CommanderCoder/pico-xb80/sharp-mz80k/mzFiles/BASIC_SP_5025_FD.asm

XOR A                  ;1200 > AF            ¯
LD (3D16H),A           ;1201   32 16 3D      2=
LD (FFFFH),A           ;1204   32 FF FF      2ÿÿ
LD HL,43FFH            ;1207   21 FF 43      !ÿC
LD D,D0H               ;120A   16 D0         Ð
INC HL                 ;120C   23            #
LD A,H                 ;120D   7C            |
CP D                   ;120E   BA            º
JR Z,121BH             ;120F   28 0A         (

LD A,FFH               ;1211   3E FF         >ÿ
LD (HL),A              ;1213   77            w
SUB (HL)               ;1214   96            
JR NZ,121BH            ;1215   20 04          
LD (HL),A              ;1217   77            w
CP (HL)                ;1218   BE            ¾
JR Z,120CH             ;1219   28 F1         (ñ
LD (4561H),HL          ;121B   22 61 45      "aE
LD (4563H),HL          ;121E   22 63 45      "cE
LD SP,HL               ;1221   F9            ù
CALL 0006H             ;1222   CD 06 00      Í
LD DE,12E2H            ;1225   11 E2 12      â
CALL 0015H             ;1228   CD 15 00      Í
CALL 1832H             ;122B   CD 32 18      Í2
LD BC,000AH            ;122E   01 0A 00      

CALL 173FH             ;1231   CD 3F 17      Í?
LD DE,4400H            ;1234   11 00 44      D
PUSH DE                ;1237   D5            Õ
CALL 16F7H             ;1238   CD F7 16      Í÷
POP DE                 ;123B   D1            Ñ
CALL 1357H             ;123C   CD 57 13      ÍW
LD DE,1326H            ;123F   11 26 13      &
CALL 0015H             ;1242   CD 15 00      Í
XOR A                  ;1245   AF            ¯
LD D,A                 ;1246   57            W
LD E,A                 ;1247   5F            _
CALL 0033H             ;1248   CD 33 00      Í3
LD DE,12FEH            ;124B   11 FE 12      þ
CALL 0030H             ;124E   CD 30 00      Í0
LD DE,12F9H            ;1251   11 F9 12      ù
CALL 1357H             ;1254   CD 57 13      ÍW
LD A,(4565H)           ;1257   3A 65 45      :eE
OR A                   ;125A   B7            ·
JP Z,1274H             ;125B   CA 74 12      Êt
LD HL,(47FFH)          ;125E   2A FF 47      *ÿG
LD A,H                 ;1261   7C            |
OR L                   ;1262   B5            µ
JP Z,1278H             ;1263   CA 78 12      Êx
LD BC,0006H            ;1266   01 06 00      
LD DE,4566H            ;1269   11 66 45      fE
LD HL,47FDH            ;126C   21 FD 47      !ýG
CALL 1799H             ;126F   CD 99 17      Í
JR 1278H               ;1272   18 04         
LD HL,(4563H)          ;1274   2A 63 45      *cE
LD SP,HL               ;1277   F9            ù
CALL 184EH             ;1278   CD 4E 18      ÍN
CALL 0009H             ;127B   CD 09 00      Í	
LD DE,4400H            ;127E   11 00 44      D
CALL 0003H             ;1281   CD 03 00      Í
CALL 13CEH             ;1284   CD CE 13      ÍÎ
CALL 1443H             ;1287   CD 43 14      ÍC
LD HL,(4457H)          ;128A   2A 57 44      *WD
LD A,L                 ;128D   7D            }
OR H                   ;128E   B4            ´
JR NZ,12A0H            ;128F   20 0F          
LD HL,4459H            ;1291   21 59 44      !YD
LD (4801H),HL          ;1294   22 01 48      "H
CALL 168BH             ;1297   CD 8B 16      Í
DEC C                  ;129A   0D            
POP HL                 ;129B   E1            á
ADD HL,DE              ;129C   19            
JP 1278H               ;129D   C3 78 12      Ãx
CALL 1987H             ;12A0   CD 87 19      Í
CALL 13C1H             ;12A3   CD C1 13      ÍÁ
CALL 17A5H             ;12A6   CD A5 17      Í¥
CP (HL)                ;12A9   BE            ¾
LD (DE),A              ;12AA   12            
JR NZ,12BEH            ;12AB   20 11          
CALL 17E8H             ;12AD   CD E8 17      Íè
EX DE,HL               ;12B0   EB            ë
CALL 1766H             ;12B1   CD 66 17      Íf
CALL 1651H             ;12B4   CD 51 16      ÍQ
CALL 189CH             ;12B7   CD 9C 18      Í
EX DE,HL               ;12BA   EB            ë
CALL 17E0H             ;12BB   CD E0 17      Íà
LD A,(4459H)           ;12BE   3A 59 44      :YD
CP 0DH                 ;12C1   FE 0D         þ
JP Z,1257H             ;12C3   CA 57 12      ÊW
CALL 17A8H             ;12C6   CD A8 17      Í¨
RL D                   ;12C9   CB 12         Ë
LD (4455H),HL          ;12CB   22 55 44      "UD
EX DE,HL               ;12CE   EB            ë
LD HL,4455H            ;12CF   21 55 44      !UD
CALL 17E8H             ;12D2   CD E8 17      Íè
CALL 1796H             ;12D5   CD 96 17      Í
CALL 189CH             ;12D8   CD 9C 18      Í
EX DE,HL               ;12DB   EB            ë
CALL 17E0H             ;12DC   CD E0 17      Íà
JP 1257H               ;12DF   C3 57 12      ÃW
JR NZ,130EH            ;12E2   20 2A          *
JR NZ,1339H            ;12E4   20 53          S
LD C,B                 ;12E6   48            H
LD B,C                 ;12E7   41            A
LD D,D                 ;12E8   52            R
LD D,B                 ;12E9   50            P
JR NZ,132EH            ;12EA   20 42          B
LD B,C                 ;12EC   41            A
LD D,E                 ;12ED   53            S
LD C,C                 ;12EE   49            I
LD B,E                 ;12EF   43            C
JR NZ,1345H            ;12F0   20 53          S
LD D,B                 ;12F2   50            P
DEC L                  ;12F3   2D            -
DEC (HL)               ;12F4   35            5
JR NC,1329H            ;12F5   30 32         02
DEC (HL)               ;12F7   35            5
DEC C                  ;12F8   0D            
LD D,D                 ;12F9   52            R
LD B,L                 ;12FA   45            E
LD B,C                 ;12FB   41            A
LD B,H                 ;12FC   44            D
LD E,C                 ;12FD   59            Y
DEC C                  ;12FE   0D            
JR NZ,1346H            ;12FF   20 45          E
LD D,D                 ;1301   52            R
LD D,D                 ;1302   52            R
LD C,A                 ;1303   4F            O
LD D,D                 ;1304   52            R
DEC C                  ;1305   0D            
JR NZ,1351H            ;1306   20 49          I
LD C,(HL)              ;1308   4E            N
DEC C                  ;1309   0D            
LD D,E                 ;130A   53            S
LD E,C                 ;130B   59            Y
LD C,(HL)              ;130C   4E            N
LD D,H                 ;130D   54            T
LD B,C                 ;130E   41            A
LD E,B                 ;130F   58            X
DEC C                  ;1310   0D            
LD C,L                 ;1311   4D            M
LD B,L                 ;1312   45            E
LD C,L                 ;1313   4D            M
LD C,A                 ;1314   4F            O
LD D,D                 ;1315   52            R
LD E,C                 ;1316   59            Y
DEC C                  ;1317   0D            
LD B,H                 ;1318   44            D
LD B,C                 ;1319   41            A
LD D,H                 ;131A   54            T
LD B,C                 ;131B   41            A
DEC C                  ;131C   0D            
LD C,L                 ;131D   4D            M
LD C,C                 ;131E   49            I
LD D,E                 ;131F   53            S
LD C,L                 ;1320   4D            M
LD B,C                 ;1321   41            A
LD D,H                 ;1322   54            T
LD B,E                 ;1323   43            C
LD C,B                 ;1324   48            H
DEC C                  ;1325   0D            
JR NZ,136AH            ;1326   20 42          B
LD E,C                 ;1328   59            Y
LD D,H                 ;1329   54            T
LD B,L                 ;132A   45            E
LD D,E                 ;132B   53            S
DEC C                  ;132C   0D            
LD B,D                 ;132D   42            B
LD D,D                 ;132E   52            R
LD B,L                 ;132F   45            E
LD B,C                 ;1330   41            A
LD C,E                 ;1331   4B            K
DEC C                  ;1332   0D            
LD SP,4636H            ;1333   31 36 46      16F
LD C,A                 ;1336   4F            O
LD D,D                 ;1337   52            R
DEC C                  ;1338   0D            
LD SP,4736H            ;1339   31 36 47      16G
LD C,A                 ;133C   4F            O
LD D,E                 ;133D   53            S
LD D,L                 ;133E   55            U
LD B,D                 ;133F   42            B
DEC C                  ;1340   0D            
LD (HL),46H            ;1341   36 46         6F
LD C,(HL)              ;1343   4E            N
DEC C                  ;1344   0D            
LD B,E                 ;1345   43            C
LD C,A                 ;1346   4F            O
LD C,(HL)              ;1347   4E            N
LD D,H                 ;1348   54            T
DEC C                  ;1349   0D            
LD B,(HL)              ;134A   46            F
LD C,C                 ;134B   49            I
LD C,H                 ;134C   4C            L
LD B,L                 ;134D   45            E
DEC C                  ;134E   0D            
LD C,A                 ;134F   4F            O
LD D,(HL)              ;1350   56            V
LD B,L                 ;1351   45            E
LD D,D                 ;1352   52            R
LD C,H                 ;1353   4C            L
LD B,C                 ;1354   41            A
LD E,C                 ;1355   59            Y
DEC C                  ;1356   0D            
CALL 0009H             ;1357   CD 09 00      Í	
JP 0015H               ;135A   C3 15 00      Ã
CALL 187CH             ;135D   CD 7C 18      Í|
CALL 1357H             ;1360   CD 57 13      ÍW
LD DE,12FFH            ;1363   11 FF 12      ÿ
CALL 0015H             ;1366   CD 15 00      Í
LD HL,(47FFH)          ;1369   2A FF 47      *ÿG
LD A,L                 ;136C   7D            }
OR H                   ;136D   B4            ´
JP Z,124BH             ;136E   CA 4B 12      ÊK
LD DE,4400H            ;1371   11 00 44      D
PUSH DE                ;1374   D5            Õ
CALL 16F7H             ;1375   CD F7 16      Í÷
LD DE,1306H            ;1378   11 06 13      
CALL 0015H             ;137B   CD 15 00      Í
POP DE                 ;137E   D1            Ñ
CALL 0015H             ;137F   CD 15 00      Í
JP 124BH               ;1382   C3 4B 12      ÃK
CALL 0009H             ;1385   CD 09 00      Í	
LD DE,132DH            ;1388   11 2D 13      -
JP 1366H               ;138B   C3 66 13      Ãf
LD DE,130AH            ;138E   11 0A 13      

JR 1396H               ;1391   18 03         
LD DE,1311H            ;1393   11 11 13      
JR 139BH               ;1396   18 03         
LD DE,1318H            ;1398   11 18 13      
JR 13A0H               ;139B   18 03         
LD DE,131DH            ;139D   11 1D 13      

JR 13A5H               ;13A0   18 03         
LD DE,1333H            ;13A2   11 33 13      3
JR 13AAH               ;13A5   18 03         
LD DE,1339H            ;13A7   11 39 13      9
JR 13AFH               ;13AA   18 03         
LD DE,1341H            ;13AC   11 41 13      A
JR 13B4H               ;13AF   18 03         
LD DE,134AH            ;13B1   11 4A 13      J
JR 13B9H               ;13B4   18 03         
LD DE,134FH            ;13B6   11 4F 13      O
JR 13BEH               ;13B9   18 03         
LD DE,1345H            ;13BB   11 45 13      E
JP 135DH               ;13BE   C3 5D 13      Ã]
XOR A                  ;13C1   AF            ¯
JR 13C6H               ;13C2   18 02         
LD A,01H               ;13C4   3E 01         >
JR 13CAH               ;13C6   18 02         
LD A,02H               ;13C8   3E 02         >
LD (4565H),A           ;13CA   32 65 45      2eE
RET                    ;13CD   C9            É
LD HL,4400H            ;13CE   21 00 44      !D
CALL 16F1H             ;13D1   CD F1 16      Íñ
EX DE,HL               ;13D4   EB            ë
LD (4457H),HL          ;13D5   22 57 44      "WD
LD HL,4459H            ;13D8   21 59 44      !YD
LD C,00H               ;13DB   0E 00         
EX DE,HL               ;13DD   EB            ë
CALL 162DH             ;13DE   CD 2D 16      Í-
CALL 1491H             ;13E1   CD 91 14      Í
RET Z                  ;13E4   C8            È
DEC DE                 ;13E5   1B            
CP 3FH                 ;13E6   FE 3F         þ?
JR NZ,13F0H            ;13E8   20 06          
LD A,85H               ;13EA   3E 85         >

LD (DE),A              ;13EC   12            
INC DE                 ;13ED   13            
JR 13E1H               ;13EE   18 F1         ñ
DEC HL                 ;13F0   2B            +
EX DE,HL               ;13F1   EB            ë
PUSH HL                ;13F2   E5            å
LD HL,14D8H            ;13F3   21 D8 14      !Ø
LD B,80H               ;13F6   06 80         
PUSH DE                ;13F8   D5            Õ
CALL 162DH             ;13F9   CD 2D 16      Í-
EX DE,HL               ;13FC   EB            ë
CALL 162DH             ;13FD   CD 2D 16      Í-
EX DE,HL               ;1400   EB            ë
CP (HL)                ;1401   BE            ¾
INC HL                 ;1402   23            #
INC DE                 ;1403   13            
JR Z,13F9H             ;1404   28 F3         (ó
DEC HL                 ;1406   2B            +
CP FFH                 ;1407   FE FF         þÿ
JP Z,1415H             ;1409   CA 15 14      Ê
ADD A,80H              ;140C   C6 80         Æ
JP C,138EH             ;140E   DA 8E 13      Ú
CP (HL)                ;1411   BE            ¾
JP Z,1427H             ;1412   CA 27 14      Ê'
INC B                  ;1415   04            
LD A,DCH               ;1416   3E DC         >Ü
CP B                   ;1418   B8            ¸
JP Z,143BH             ;1419   CA 3B 14      Ê;
LD A,7FH               ;141C   3E 7F         >
CP (HL)                ;141E   BE            ¾
INC HL                 ;141F   23            #
JP NC,141EH            ;1420   D2 1E 14      Ò

POP DE                 ;1423   D1            Ñ
JP 13F8H               ;1424   C3 F8 13      Ãø
POP AF                 ;1427   F1            ñ
POP HL                 ;1428   E1            á
LD (HL),B              ;1429   70            p
INC HL                 ;142A   23            #
EX DE,HL               ;142B   EB            ë
LD A,B                 ;142C   78            x
CP 82H                 ;142D   FE 82         þ
JP NC,13E1H            ;142F   D2 E1 13      Òá
CALL 14C5H             ;1432   CD C5 14      ÍÅ
CP 3AH                 ;1435   FE 3A         þ:
JP Z,13E1H             ;1437   CA E1 13      Êá
RET                    ;143A   C9            É
POP DE                 ;143B   D1            Ñ
POP HL                 ;143C   E1            á
INC DE                 ;143D   13            
INC HL                 ;143E   23            #
EX DE,HL               ;143F   EB            ë
JP 13E1H               ;1440   C3 E1 13      Ãá
LD HL,(4457H)          ;1443   2A 57 44      *WD
LD DE,4400H            ;1446   11 00 44      D
LD C,B2H               ;1449   0E B2         ²
CALL 16F9H             ;144B   CD F9 16      Íù
LD A,20H               ;144E   3E 20         > 
LD (DE),A              ;1450   12            
INC DE                 ;1451   13            
LD HL,4459H            ;1452   21 59 44      !YD
CALL 1491H             ;1455   CD 91 14      Í
RET Z                  ;1458   C8            È
SUB 80H                ;1459   D6 80         Ö
JP M,1455H             ;145B   FA 55 14      úU
DEC C                  ;145E   0D            
PUSH AF                ;145F   F5            õ
DEC DE                 ;1460   1B            
PUSH HL                ;1461   E5            å
LD HL,14D8H            ;1462   21 D8 14      !Ø
OR A                   ;1465   B7            ·
JP Z,1475H             ;1466   CA 75 14      Êu
PUSH AF                ;1469   F5            õ
LD A,7FH               ;146A   3E 7F         >
CP (HL)                ;146C   BE            ¾
INC HL                 ;146D   23            #
JR NC,146CH            ;146E   30 FC         0ü
POP AF                 ;1470   F1            ñ
DEC A                  ;1471   3D            =
JP 1465H               ;1472   C3 65 14      Ãe
CALL 14BAH             ;1475   CD BA 14      Íº
OR A                   ;1478   B7            ·
JP P,1475H             ;1479   F2 75 14      òu
DEC DE                 ;147C   1B            
AND 7FH                ;147D   E6 7F         æ
LD (DE),A              ;147F   12            
INC DE                 ;1480   13            
POP HL                 ;1481   E1            á
POP AF                 ;1482   F1            ñ
CP 02H                 ;1483   FE 02         þ
JP NC,1455H            ;1485   D2 55 14      ÒU
CALL 14C5H             ;1488   CD C5 14      ÍÅ
CP 3AH                 ;148B   FE 3A         þ:
JP Z,1455H             ;148D   CA 55 14      ÊU
RET                    ;1490   C9            É
CALL 14BAH             ;1491   CD BA 14      Íº
RET Z                  ;1494   C8            È
CALL 14A5H             ;1495   CD A5 14      Í¥
JR Z,1491H             ;1498   28 F7         (÷
CP 22H                 ;149A   FE 22         þ"
RET NZ                 ;149C   C0            À
CALL 14B1H             ;149D   CD B1 14      Í±
CP 0DH                 ;14A0   FE 0D         þ
JR NZ,1491H            ;14A2   20 ED          í
RET                    ;14A4   C9            É
CP 20H                 ;14A5   FE 20         þ 
RET Z                  ;14A7   C8            È
CP FFH                 ;14A8   FE FF         þÿ
RET Z                  ;14AA   C8            È
CP 28H                 ;14AB   FE 28         þ(
RET Z                  ;14AD   C8            È
CP 29H                 ;14AE   FE 29         þ)
RET                    ;14B0   C9            É
CALL 14BAH             ;14B1   CD BA 14      Íº
RET Z                  ;14B4   C8            È
CP 22H                 ;14B5   FE 22         þ"
JR NZ,14B1H            ;14B7   20 F8          ø
RET                    ;14B9   C9            É
LD A,(HL)              ;14BA   7E            ~
LD (DE),A              ;14BB   12            
INC HL                 ;14BC   23            #
INC DE                 ;14BD   13            
INC C                  ;14BE   0C            

JP Z,1398H             ;14BF   CA 98 13      Ê
CP 0DH                 ;14C2   FE 0D         þ
RET                    ;14C4   C9            É
CALL 14BAH             ;14C5   CD BA 14      Íº
RET Z                  ;14C8   C8            È
CP 3AH                 ;14C9   FE 3A         þ:
RET Z                  ;14CB   C8            È
CP 22H                 ;14CC   FE 22         þ"
JR NZ,14C5H            ;14CE   20 F5          õ
CALL 14B1H             ;14D0   CD B1 14      Í±
CP 0DH                 ;14D3   FE 0D         þ
JR NZ,14C5H            ;14D5   20 EE          î
RET                    ;14D7   C9            É
LD D,D                 ;14D8   52            R
LD B,L                 ;14D9   45            E
CALL 4144H             ;14DA   CD 44 41      ÍDA
LD D,H                 ;14DD   54            T
POP BC                 ;14DE   C1            Á
LD C,H                 ;14DF   4C            L
LD C,C                 ;14E0   49            I
LD D,E                 ;14E1   53            S
CALL NC,5552H          ;14E2   D4 52 55      ÔRU
ADC A,4EH              ;14E5   CE 4E         ÎN
LD B,L                 ;14E7   45            E
RST 10H                ;14E8   D7            ×
LD D,B                 ;14E9   50            P
LD D,D                 ;14EA   52            R
LD C,C                 ;14EB   49            I
LD C,(HL)              ;14EC   4E            N
CALL NC,454CH          ;14ED   D4 4C 45      ÔLE
CALL NC,4F46H          ;14F0   D4 46 4F      ÔFO
JP NC,C649H            ;14F3   D2 49 C6      ÒIÆ
LD B,A                 ;14F6   47            G
LD C,A                 ;14F7   4F            O
LD D,H                 ;14F8   54            T
RST 08H                ;14F9   CF            Ï
LD D,D                 ;14FA   52            R
LD B,L                 ;14FB   45            E
LD B,C                 ;14FC   41            A
CALL NZ,4F47H          ;14FD   C4 47 4F      ÄGO
LD D,E                 ;1500   53            S
LD D,L                 ;1501   55            U
JP NZ,4552H            ;1502   C2 52 45      ÂRE
LD D,H                 ;1505   54            T
LD D,L                 ;1506   55            U
LD D,D                 ;1507   52            R
ADC A,4EH              ;1508   CE 4E         ÎN
LD B,L                 ;150A   45            E
LD E,B                 ;150B   58            X
CALL NC,5453H          ;150C   D4 53 54      ÔST
LD C,A                 ;150F   4F            O
RET NC                 ;1510   D0            Ð
LD B,L                 ;1511   45            E
LD C,(HL)              ;1512   4E            N
CALL NZ,CE4FH          ;1513   C4 4F CE      ÄOÎ
LD C,H                 ;1516   4C            L
LD C,A                 ;1517   4F            O
LD B,C                 ;1518   41            A
CALL NZ,4153H          ;1519   C4 53 41      ÄSA
LD D,(HL)              ;151C   56            V
PUSH BC                ;151D   C5            Å
LD D,(HL)              ;151E   56            V
LD B,L                 ;151F   45            E
LD D,D                 ;1520   52            R
LD C,C                 ;1521   49            I
LD B,(HL)              ;1522   46            F
EXX                    ;1523   D9            Ù
LD D,B                 ;1524   50            P
LD C,A                 ;1525   4F            O
LD C,E                 ;1526   4B            K
PUSH BC                ;1527   C5            Å
LD B,H                 ;1528   44            D
LD C,C                 ;1529   49            I
CALL 4544H             ;152A   CD 44 45      ÍDE
LD B,(HL)              ;152D   46            F
JR NZ,1576H            ;152E   20 46          F
ADC A,49H              ;1530   CE 49         ÎI
LD C,(HL)              ;1532   4E            N
LD D,B                 ;1533   50            P
LD D,L                 ;1534   55            U
CALL NC,4552H          ;1535   D4 52 45      ÔRE
LD D,E                 ;1538   53            S
LD D,H                 ;1539   54            T
LD C,A                 ;153A   4F            O
LD D,D                 ;153B   52            R
PUSH BC                ;153C   C5            Å
LD B,E                 ;153D   43            C
LD C,H                 ;153E   4C            L
JP NC,554DH            ;153F   D2 4D 55      ÒMU
LD D,E                 ;1542   53            S
LD C,C                 ;1543   49            I
JP 4554H               ;1544   C3 54 45      ÃTE
LD C,L                 ;1547   4D            M
LD D,B                 ;1548   50            P
RST 08H                ;1549   CF            Ï
LD D,L                 ;154A   55            U
LD D,E                 ;154B   53            S
LD D,D                 ;154C   52            R
XOR B                  ;154D   A8            ¨
LD D,A                 ;154E   57            W
LD C,A                 ;154F   4F            O
LD D,B                 ;1550   50            P
LD B,L                 ;1551   45            E
ADC A,52H              ;1552   CE 52         ÎR
LD C,A                 ;1554   4F            O
LD D,B                 ;1555   50            P
LD B,L                 ;1556   45            E
ADC A,43H              ;1557   CE 43         ÎC
LD C,H                 ;1559   4C            L
LD C,A                 ;155A   4F            O
LD D,E                 ;155B   53            S
PUSH BC                ;155C   C5            Å
LD B,D                 ;155D   42            B
LD E,C                 ;155E   59            Y
PUSH BC                ;155F   C5            Å
LD C,H                 ;1560   4C            L
LD C,C                 ;1561   49            I
LD C,L                 ;1562   4D            M
LD C,C                 ;1563   49            I
CALL NC,4F43H          ;1564   D4 43 4F      ÔCO
LD C,(HL)              ;1567   4E            N
CALL NC,4553H          ;1568   D4 53 45      ÔSE
CALL NC,4552H          ;156B   D4 52 45      ÔRE
LD D,E                 ;156E   53            S
LD B,L                 ;156F   45            E
CALL NC,4547H          ;1570   D4 47 45      ÔGE
CALL NC,4E49H          ;1573   D4 49 4E      ÔIN
LD D,B                 ;1576   50            P
AND E                  ;1577   A3            £
LD C,A                 ;1578   4F            O
LD D,L                 ;1579   55            U
LD D,H                 ;157A   54            T
AND E                  ;157B   A3            £
RST 38H                ;157C   FF            ÿ
RST 38H                ;157D   FF            ÿ
RST 38H                ;157E   FF            ÿ
RST 38H                ;157F   FF            ÿ
RST 38H                ;1580   FF            ÿ
LD D,H                 ;1581   54            T
LD C,B                 ;1582   48            H
LD B,L                 ;1583   45            E
ADC A,54H              ;1584   CE 54         ÎT
RST 08H                ;1586   CF            Ï
LD D,E                 ;1587   53            S
LD D,H                 ;1588   54            T
LD B,L                 ;1589   45            E
RET NC                 ;158A   D0            Ð
LD A,BCH               ;158B   3E BC         >¼
INC A                  ;158D   3C            <
CP (HL)                ;158E   BE            ¾
DEC A                  ;158F   3D            =
CP H                   ;1590   BC            ¼
INC A                  ;1591   3C            <
CP L                   ;1592   BD            ½
DEC A                  ;1593   3D            =
CP (HL)                ;1594   BE            ¾
LD A,BDH               ;1595   3E BD         >½
CP L                   ;1597   BD            ½
CP (HL)                ;1598   BE            ¾
CP H                   ;1599   BC            ¼
LD B,C                 ;159A   41            A
LD C,(HL)              ;159B   4E            N
CALL NZ,D24FH          ;159C   C4 4F D2      ÄOÒ
LD C,(HL)              ;159F   4E            N
LD C,A                 ;15A0   4F            O
CALL NC,ADABH          ;15A1   D4 AB AD      Ô«­
XOR D                  ;15A4   AA            ª
XOR A                  ;15A5   AF            ¯
LD C,H                 ;15A6   4C            L
LD B,L                 ;15A7   45            E
LD B,(HL)              ;15A8   46            F
LD D,H                 ;15A9   54            T
INC H                  ;15AA   24            $
XOR B                  ;15AB   A8            ¨
LD D,D                 ;15AC   52            R
LD C,C                 ;15AD   49            I
LD B,A                 ;15AE   47            G
LD C,B                 ;15AF   48            H
LD D,H                 ;15B0   54            T
INC H                  ;15B1   24            $
XOR B                  ;15B2   A8            ¨
LD C,L                 ;15B3   4D            M
LD C,C                 ;15B4   49            I
LD B,H                 ;15B5   44            D
INC H                  ;15B6   24            $
XOR B                  ;15B7   A8            ¨
LD C,H                 ;15B8   4C            L
LD B,L                 ;15B9   45            E
LD C,(HL)              ;15BA   4E            N
XOR B                  ;15BB   A8            ¨
LD B,E                 ;15BC   43            C
LD C,B                 ;15BD   48            H
LD D,D                 ;15BE   52            R
INC H                  ;15BF   24            $
XOR B                  ;15C0   A8            ¨
LD D,E                 ;15C1   53            S
LD D,H                 ;15C2   54            T
LD D,D                 ;15C3   52            R
INC H                  ;15C4   24            $
XOR B                  ;15C5   A8            ¨
LD B,C                 ;15C6   41            A
LD D,E                 ;15C7   53            S
LD B,E                 ;15C8   43            C
XOR B                  ;15C9   A8            ¨
LD D,(HL)              ;15CA   56            V
LD B,C                 ;15CB   41            A
LD C,H                 ;15CC   4C            L
XOR B                  ;15CD   A8            ¨
LD D,B                 ;15CE   50            P
LD B,L                 ;15CF   45            E
LD B,L                 ;15D0   45            E
LD C,E                 ;15D1   4B            K
XOR B                  ;15D2   A8            ¨
LD D,H                 ;15D3   54            T
LD B,C                 ;15D4   41            A
LD B,D                 ;15D5   42            B
XOR B                  ;15D6   A8            ¨
LD D,E                 ;15D7   53            S
LD D,B                 ;15D8   50            P
LD B,E                 ;15D9   43            C
XOR B                  ;15DA   A8            ¨
LD D,E                 ;15DB   53            S
LD C,C                 ;15DC   49            I
LD E,D                 ;15DD   5A            Z
PUSH BC                ;15DE   C5            Å
RST 38H                ;15DF   FF            ÿ
RST 38H                ;15E0   FF            ÿ
RST 38H                ;15E1   FF            ÿ
SBC A,52H              ;15E2   DE 52         ÞR
LD C,(HL)              ;15E4   4E            N
LD B,H                 ;15E5   44            D
XOR B                  ;15E6   A8            ¨
LD D,E                 ;15E7   53            S
LD C,C                 ;15E8   49            I
LD C,(HL)              ;15E9   4E            N
XOR B                  ;15EA   A8            ¨
LD B,E                 ;15EB   43            C
LD C,A                 ;15EC   4F            O
LD D,E                 ;15ED   53            S
XOR B                  ;15EE   A8            ¨
LD D,H                 ;15EF   54            T
LD B,C                 ;15F0   41            A
LD C,(HL)              ;15F1   4E            N
XOR B                  ;15F2   A8            ¨
LD B,C                 ;15F3   41            A
LD D,H                 ;15F4   54            T
LD C,(HL)              ;15F5   4E            N
XOR B                  ;15F6   A8            ¨
LD B,L                 ;15F7   45            E
LD E,B                 ;15F8   58            X
LD D,B                 ;15F9   50            P
XOR B                  ;15FA   A8            ¨
LD C,C                 ;15FB   49            I
LD C,(HL)              ;15FC   4E            N
LD D,H                 ;15FD   54            T
XOR B                  ;15FE   A8            ¨
LD C,H                 ;15FF   4C            L
LD C,A                 ;1600   4F            O
LD B,A                 ;1601   47            G
XOR B                  ;1602   A8            ¨
LD C,H                 ;1603   4C            L
LD C,(HL)              ;1604   4E            N
XOR B                  ;1605   A8            ¨
LD B,C                 ;1606   41            A
LD B,D                 ;1607   42            B
LD D,E                 ;1608   53            S
XOR B                  ;1609   A8            ¨
LD D,E                 ;160A   53            S
LD B,A                 ;160B   47            G
LD C,(HL)              ;160C   4E            N
XOR B                  ;160D   A8            ¨
LD D,E                 ;160E   53            S
LD D,C                 ;160F   51            Q
LD D,D                 ;1610   52            R
XOR B                  ;1611   A8            ¨
RST 38H                ;1612   FF            ÿ
RST 38H                ;1613   FF            ÿ
POP BC                 ;1614   C1            Á
NOP                    ;1615   00            
NOP                    ;1616   00            
NOP                    ;1617   00            
ADD A,B                ;1618   80            
ADD A,B                ;1619   80            
NOP                    ;161A   00            
NOP                    ;161B   00            
NOP                    ;161C   00            
NOP                    ;161D   00            
LD B,C                 ;161E   41            A
NOP                    ;161F   00            
NOP                    ;1620   00            
NOP                    ;1621   00            
ADD A,B                ;1622   80            
JP NZ,DAA1H            ;1623   C2 A1 DA      Â¡Ú
RRCA                   ;1626   0F            
RET                    ;1627   C9            É
LD HL,(4801H)          ;1628   2A 01 48      *H
DEC HL                 ;162B   2B            +
INC HL                 ;162C   23            #
LD A,(HL)              ;162D   7E            ~
CP 20H                 ;162E   FE 20         þ 
RET NZ                 ;1630   C0            À
JR 162CH               ;1631   18 F9         ù
PUSH AF                ;1633   F5            õ
LD A,0DH               ;1634   3E 0D         >
CP (HL)                ;1636   BE            ¾
INC HL                 ;1637   23            #
JR NZ,1636H            ;1638   20 FC          ü
POP AF                 ;163A   F1            ñ
RET                    ;163B   C9            É
INC HL                 ;163C   23            #
CALL 1829H             ;163D   CD 29 18      Í)
RET Z                  ;1640   C8            È
CP 22H                 ;1641   FE 22         þ"
JR NZ,163CH            ;1643   20 F7          ÷
CALL 162CH             ;1645   CD 2C 16      Í,
CP 0DH                 ;1648   FE 0D         þ
RET Z                  ;164A   C8            È
CP 22H                 ;164B   FE 22         þ"
JR NZ,1645H            ;164D   20 F6          ö
JR 163CH               ;164F   18 EB         ë
LD A,C                 ;1651   79            y
CPL                    ;1652   2F            /
LD C,A                 ;1653   4F            O
LD A,B                 ;1654   78            x
CPL                    ;1655   2F            /
LD B,A                 ;1656   47            G
INC BC                 ;1657   03            
RET                    ;1658   C9            É
CALL 162DH             ;1659   CD 2D 16      Í-
SUB 30H                ;165C   D6 30         Ö0
CP 0AH                 ;165E   FE 0A         þ

LD A,(HL)              ;1660   7E            ~
RET                    ;1661   C9            É
LD A,H                 ;1662   7C            |
SUB D                  ;1663   92            
RET NZ                 ;1664   C0            À
LD A,L                 ;1665   7D            }
SUB E                  ;1666   93            
RET                    ;1667   C9            É
LD A,E                 ;1668   7B            {
SUB L                  ;1669   95            
LD L,A                 ;166A   6F            o
LD A,D                 ;166B   7A            z
SBC A,H                ;166C   9C            
LD H,A                 ;166D   67            g
RET                    ;166E   C9            É
POP HL                 ;166F   E1            á
EX (SP),HL             ;1670   E3            ã
PUSH AF                ;1671   F5            õ
LD A,(HL)              ;1672   7E            ~
INC HL                 ;1673   23            #
LD H,(HL)              ;1674   66            f
LD L,A                 ;1675   6F            o
POP AF                 ;1676   F1            ñ
EX (SP),HL             ;1677   E3            ã
RET                    ;1678   C9            É
POP HL                 ;1679   E1            á
EX (SP),HL             ;167A   E3            ã
INC HL                 ;167B   23            #
INC HL                 ;167C   23            #
EX (SP),HL             ;167D   E3            ã
RET                    ;167E   C9            É
LD HL,(4644H)          ;167F   2A 44 46      *DF
INC HL                 ;1682   23            #
INC HL                 ;1683   23            #
INC HL                 ;1684   23            #
INC HL                 ;1685   23            #
INC HL                 ;1686   23            #
RET                    ;1687   C9            É
LD HL,(4801H)          ;1688   2A 01 48      *H
CALL 162DH             ;168B   CD 2D 16      Í-
EX (SP),HL             ;168E   E3            ã
CP (HL)                ;168F   BE            ¾
INC HL                 ;1690   23            #
JP NZ,1671H            ;1691   C2 71 16      Âq
INC HL                 ;1694   23            #
JR 16A2H               ;1695   18 0B         

LD HL,(4801H)          ;1697   2A 01 48      *H
CALL 162DH             ;169A   CD 2D 16      Í-
EX (SP),HL             ;169D   E3            ã
CP (HL)                ;169E   BE            ¾
JP NZ,138EH            ;169F   C2 8E 13      Â
INC HL                 ;16A2   23            #
EX (SP),HL             ;16A3   E3            ã
JP 162CH               ;16A4   C3 2C 16      Ã,
XOR A                  ;16A7   AF            ¯
CP H                   ;16A8   BC            ¼
JR Z,16B0H             ;16A9   28 05         (
EX DE,HL               ;16AB   EB            ë
CP H                   ;16AC   BC            ¼
JP NZ,1670H            ;16AD   C2 70 16      Âp
LD A,L                 ;16B0   7D            }
LD L,H                 ;16B1   6C            l
OR A                   ;16B2   B7            ·
JR NZ,16B9H            ;16B3   20 04          
EX DE,HL               ;16B5   EB            ë
JP 167AH               ;16B6   C3 7A 16      Ãz
SRL A                  ;16B9   CB 3F         Ë?
JR NC,16C1H            ;16BB   30 04         0
ADD HL,DE              ;16BD   19            
JP C,1670H             ;16BE   DA 70 16      Úp
SLA E                  ;16C1   CB 23         Ë#
RL D                   ;16C3   CB 12         Ë
JP 16B2H               ;16C5   C3 B2 16      Ã²
CALL 16A7H             ;16C8   CD A7 16      Í
SBC A,B                ;16CB   98            
INC DE                 ;16CC   13            
RET                    ;16CD   C9            É
LD DE,0000H            ;16CE   11 00 00      
CALL 1659H             ;16D1   CD 59 16      ÍY
JP NC,167AH            ;16D4   D2 7A 16      Òz
PUSH HL                ;16D7   E5            å
LD HL,000AH            ;16D8   21 0A 00      !

CALL 16A7H             ;16DB   CD A7 16      Í
LD L,A                 ;16DE   6F            o
LD D,E1H               ;16DF   16 E1         á
LD A,(HL)              ;16E1   7E            ~
AND 0FH                ;16E2   E6 0F         æ
ADD A,E                ;16E4   83            
LD E,A                 ;16E5   5F            _
LD A,D                 ;16E6   7A            z
ADC A,00H              ;16E7   CE 00         Î
LD D,A                 ;16E9   57            W
JP C,1670H             ;16EA   DA 70 16      Úp
INC HL                 ;16ED   23            #
JP 16D1H               ;16EE   C3 D1 16      ÃÑ
CALL 16CEH             ;16F1   CD CE 16      ÍÎ
ADC A,(HL)             ;16F4   8E            
INC DE                 ;16F5   13            
RET                    ;16F6   C9            É
LD C,00H               ;16F7   0E 00         
LD A,20H               ;16F9   3E 20         > 
LD (DE),A              ;16FB   12            
INC DE                 ;16FC   13            
PUSH DE                ;16FD   D5            Õ
LD B,00H               ;16FE   06 00         
LD DE,2710H            ;1700   11 10 27      '
CALL 1722H             ;1703   CD 22 17      Í"
LD DE,03E8H            ;1706   11 E8 03      è
CALL 1722H             ;1709   CD 22 17      Í"
LD DE,0064H            ;170C   11 64 00      d
CALL 1722H             ;170F   CD 22 17      Í"
LD DE,000AH            ;1712   11 0A 00      

CALL 1722H             ;1715   CD 22 17      Í"
LD A,L                 ;1718   7D            }
POP DE                 ;1719   D1            Ñ
OR 30H                 ;171A   F6 30         ö0
LD (DE),A              ;171C   12            
INC DE                 ;171D   13            
LD A,0DH               ;171E   3E 0D         >
LD (DE),A              ;1720   12            
RET                    ;1721   C9            É
LD A,FFH               ;1722   3E FF         >ÿ
INC A                  ;1724   3C            <
OR A                   ;1725   B7            ·
SBC HL,DE              ;1726   ED 52         íR
JR NC,1724H            ;1728   30 FA         0ú
ADD HL,DE              ;172A   19            
OR A                   ;172B   B7            ·
JR NZ,1731H            ;172C   20 03          
OR B                   ;172E   B0            °
RET Z                  ;172F   C8            È
XOR A                  ;1730   AF            ¯
INC B                  ;1731   04            
OR 30H                 ;1732   F6 30         ö0
POP DE                 ;1734   D1            Ñ
EX (SP),HL             ;1735   E3            ã
LD (HL),A              ;1736   77            w
INC HL                 ;1737   23            #
EX (SP),HL             ;1738   E3            ã
PUSH DE                ;1739   D5            Õ
INC C                  ;173A   0C            

RET                    ;173B   C9            É
LD BC,0000H            ;173C   01 00 00      
LD HL,(4644H)          ;173F   2A 44 46      *DF
ADD HL,BC              ;1742   09            	
JP C,1393H             ;1743   DA 93 13      Ú
EX DE,HL               ;1746   EB            ë
LD HL,FF9CH            ;1747   21 9C FF      !ÿ
ADD HL,SP              ;174A   39            9
XOR A                  ;174B   AF            ¯
SBC HL,DE              ;174C   ED 52         íR
RET NC                 ;174E   D0            Ð
JP 1393H               ;174F   C3 93 13      Ã
PUSH HL                ;1752   E5            å
PUSH DE                ;1753   D5            Õ
CALL 173FH             ;1754   CD 3F 17      Í?
POP DE                 ;1757   D1            Ñ
POP HL                 ;1758   E1            á
RET                    ;1759   C9            É
LD E,(HL)              ;175A   5E            ^
INC HL                 ;175B   23            #
LD D,(HL)              ;175C   56            V
INC HL                 ;175D   23            #
LD A,(HL)              ;175E   7E            ~
INC HL                 ;175F   23            #
LD H,(HL)              ;1760   66            f
LD L,A                 ;1761   6F            o
EX DE,HL               ;1762   EB            ë
LD A,L                 ;1763   7D            }
OR H                   ;1764   B4            ´
RET                    ;1765   C9            É
PUSH BC                ;1766   C5            Å
PUSH HL                ;1767   E5            å
PUSH DE                ;1768   D5            Õ
EX DE,HL               ;1769   EB            ë
ADD HL,BC              ;176A   09            	
EX DE,HL               ;176B   EB            ë
CALL 167FH             ;176C   CD 7F 16      Í
LD A,L                 ;176F   7D            }
SUB E                  ;1770   93            
LD C,A                 ;1771   4F            O
LD A,H                 ;1772   7C            |
SBC A,D                ;1773   9A            
LD B,A                 ;1774   47            G
INC BC                 ;1775   03            
POP HL                 ;1776   E1            á
PUSH HL                ;1777   E5            å
EX DE,HL               ;1778   EB            ë
JP 179CH               ;1779   C3 9C 17      Ã
CALL 1752H             ;177C   CD 52 17      ÍR
PUSH BC                ;177F   C5            Å
PUSH HL                ;1780   E5            å
PUSH DE                ;1781   D5            Õ
CALL 167FH             ;1782   CD 7F 16      Í
PUSH HL                ;1785   E5            å
ADD HL,BC              ;1786   09            	
EX (SP),HL             ;1787   E3            ã
LD A,L                 ;1788   7D            }
SUB E                  ;1789   93            
LD C,A                 ;178A   4F            O
LD A,H                 ;178B   7C            |
SBC A,D                ;178C   9A            
LD B,A                 ;178D   47            G
INC BC                 ;178E   03            
POP DE                 ;178F   D1            Ñ
LDDR                   ;1790   ED B8         í¸
POP DE                 ;1792   D1            Ñ
POP HL                 ;1793   E1            á
POP BC                 ;1794   C1            Á
RET                    ;1795   C9            É
CALL 177CH             ;1796   CD 7C 17      Í|
PUSH BC                ;1799   C5            Å
PUSH HL                ;179A   E5            å
PUSH DE                ;179B   D5            Õ
LD A,C                 ;179C   79            y
OR B                   ;179D   B0            °
JR Z,17A2H             ;179E   28 02         (
LDIR                   ;17A0   ED B0         í°
JP 1792H               ;17A2   C3 92 17      Ã
LD (462EH),HL          ;17A5   22 2E 46      ".F
LD HL,4806H            ;17A8   21 06 48      !H
PUSH HL                ;17AB   E5            å
CALL 175AH             ;17AC   CD 5A 17      ÍZ
JP Z,166FH             ;17AF   CA 6F 16      Êo
PUSH HL                ;17B2   E5            å
LD HL,(462EH)          ;17B3   2A 2E 46      *.F
CALL 1662H             ;17B6   CD 62 16      Íb
POP HL                 ;17B9   E1            á
JP Z,1679H             ;17BA   CA 79 16      Êy
JP C,1679H             ;17BD   DA 79 16      Úy
POP AF                 ;17C0   F1            ñ
JP 17ABH               ;17C1   C3 AB 17      Ã«
PUSH HL                ;17C4   E5            å
LD E,(HL)              ;17C5   5E            ^
INC HL                 ;17C6   23            #
LD D,(HL)              ;17C7   56            V
LD A,E                 ;17C8   7B            {
OR D                   ;17C9   B2            ²
JP Z,166FH             ;17CA   CA 6F 16      Êo
LD HL,(4630H)          ;17CD   2A 30 46      *0F
CALL 1662H             ;17D0   CD 62 16      Íb
POP HL                 ;17D3   E1            á
INC HL                 ;17D4   23            #
INC HL                 ;17D5   23            #
JP 167AH               ;17D6   C3 7A 16      Ãz
ADD HL,BC              ;17D9   09            	
EX DE,HL               ;17DA   EB            ë
POP HL                 ;17DB   E1            á
LD (HL),E              ;17DC   73            s
INC HL                 ;17DD   23            #
LD (HL),D              ;17DE   72            r
EX DE,HL               ;17DF   EB            ë
PUSH HL                ;17E0   E5            å
CALL 175AH             ;17E1   CD 5A 17      ÍZ
JR NZ,17D9H            ;17E4   20 F3          ó
POP HL                 ;17E6   E1            á
RET                    ;17E7   C9            É
PUSH HL                ;17E8   E5            å
LD BC,0004H            ;17E9   01 04 00      
ADD HL,BC              ;17EC   09            	
CALL 17F6H             ;17ED   CD F6 17      Íö
INC BC                 ;17F0   03            
POP HL                 ;17F1   E1            á
RET                    ;17F2   C9            É
LD BC,0000H            ;17F3   01 00 00      
PUSH HL                ;17F6   E5            å
LD A,0DH               ;17F7   3E 0D         >
CP (HL)                ;17F9   BE            ¾
INC HL                 ;17FA   23            #
INC BC                 ;17FB   03            
JR NZ,17F9H            ;17FC   20 FB          û
DEC BC                 ;17FE   0B            

POP HL                 ;17FF   E1            á
RET                    ;1800   C9            É
LD A,E                 ;1801   7B            {
EX DE,HL               ;1802   EB            ë
LD HL,(4642H)          ;1803   2A 42 46      *BF
INC A                  ;1806   3C            <
DEC A                  ;1807   3D            =
CALL NZ,1633H          ;1808   C4 33 16      Ä3
JR NZ,1807H            ;180B   20 FA          ú
EX DE,HL               ;180D   EB            ë
RET                    ;180E   C9            É
LD A,D                 ;180F   7A            z
OR A                   ;1810   B7            ·
RET NZ                 ;1811   C0            À
JR 1817H               ;1812   18 03         
LD A,D                 ;1814   7A            z
OR A                   ;1815   B7            ·
RET Z                  ;1816   C8            È
JP 139DH               ;1817   C3 9D 13      Ã
LD HL,(4644H)          ;181A   2A 44 46      *DF
EX DE,HL               ;181D   EB            ë
LD BC,0005H            ;181E   01 05 00      
LDIR                   ;1821   ED B0         í°
RET                    ;1823   C9            É
LD HL,(4644H)          ;1824   2A 44 46      *DF
JR 181EH               ;1827   18 F5         õ
CALL 162DH             ;1829   CD 2D 16      Í-
CP 0DH                 ;182C   FE 0D         þ
RET Z                  ;182E   C8            È
CP 3AH                 ;182F   FE 3A         þ:
RET                    ;1831   C9            É
LD HL,0000H            ;1832   21 00 00      !
LD (4632H),HL          ;1835   22 32 46      "2F
LD HL,4806H            ;1838   21 06 48      !H
CALL 1896H             ;183B   CD 96 18      Í
LD (4634H),HL          ;183E   22 34 46      "4F
XOR A                  ;1841   AF            ¯
LD (29B8H),A           ;1842   32 B8 29      2¸)
CALL 13C1H             ;1845   CD C1 13      ÍÁ
CALL 1857H             ;1848   CD 57 18      ÍW
CALL 187CH             ;184B   CD 7C 18      Í|
LD HL,47FDH            ;184E   21 FD 47      !ýG
CALL 1896H             ;1851   CD 96 18      Í
JP 1896H               ;1854   C3 96 18      Ã
LD HL,(4634H)          ;1857   2A 34 46      *4F
LD B,09H               ;185A   06 09         	
CALL 1896H             ;185C   CD 96 18      Í
DJNZ 185CH             ;185F   10 FB         û
LD DE,4636H            ;1861   11 36 46      6F
LD HL,(4634H)          ;1864   2A 34 46      *4F
EX DE,HL               ;1867   EB            ë
LD B,07H               ;1868   06 07         
INC DE                 ;186A   13            
INC DE                 ;186B   13            
LD (HL),E              ;186C   73            s
INC HL                 ;186D   23            #
LD (HL),D              ;186E   72            r
INC HL                 ;186F   23            #
DJNZ 186AH             ;1870   10 F8         ø
LD HL,(4642H)          ;1872   2A 42 46      *BF
CALL 1896H             ;1875   CD 96 18      Í
LD (4644H),HL          ;1878   22 44 46      "DF
RET                    ;187B   C9            É
LD HL,47F0H            ;187C   21 F0 47      !ðG
LD (464AH),HL          ;187F   22 4A 46      "JF
LD HL,4787H            ;1882   21 87 47      !G
LD (4648H),HL          ;1885   22 48 46      "HF
LD HL,466AH            ;1888   21 6A 46      !jF
LD (4646H),HL          ;188B   22 46 46      "FF
LD HL,4803H            ;188E   21 03 48      !H
CALL 1896H             ;1891   CD 96 18      Í
LD (HL),A              ;1894   77            w
RET                    ;1895   C9            É
XOR A                  ;1896   AF            ¯
LD (HL),A              ;1897   77            w
INC HL                 ;1898   23            #
LD (HL),A              ;1899   77            w
INC HL                 ;189A   23            #
RET                    ;189B   C9            É
PUSH HL                ;189C   E5            å
LD A,E                 ;189D   7B            {
EX AF,AF'              ;189E   08            
LD A,D                 ;189F   7A            z
LD HL,4644H            ;18A0   21 44 46      !DF
LD E,(HL)              ;18A3   5E            ^
INC HL                 ;18A4   23            #
LD D,(HL)              ;18A5   56            V
CP D                   ;18A6   BA            º
JP C,18B3H             ;18A7   DA B3 18      Ú³
JP NZ,18BFH            ;18AA   C2 BF 18      Â¿
EX AF,AF'              ;18AD   08            
CP E                   ;18AE   BB            »
JP NC,18BEH            ;18AF   D2 BE 18      Ò¾
EX AF,AF'              ;18B2   08            
EX DE,HL               ;18B3   EB            ë
ADD HL,BC              ;18B4   09            	
EX DE,HL               ;18B5   EB            ë
LD (HL),D              ;18B6   72            r
DEC HL                 ;18B7   2B            +
LD (HL),E              ;18B8   73            s
DEC HL                 ;18B9   2B            +
DEC HL                 ;18BA   2B            +
JP 18A3H               ;18BB   C3 A3 18      Ã£
EX AF,AF'              ;18BE   08            
LD D,A                 ;18BF   57            W
EX AF,AF'              ;18C0   08            
LD E,A                 ;18C1   5F            _
POP HL                 ;18C2   E1            á
RET                    ;18C3   C9            É
CALL 162DH             ;18C4   CD 2D 16      Í-
LD BC,0000H            ;18C7   01 00 00      
LD DE,0D2CH            ;18CA   11 2C 0D      ,
CP 22H                 ;18CD   FE 22         þ"
JR NZ,18D3H            ;18CF   20 02          
LD E,A                 ;18D1   5F            _
INC HL                 ;18D2   23            #
PUSH HL                ;18D3   E5            å
LD A,(HL)              ;18D4   7E            ~
CP D                   ;18D5   BA            º
JR Z,18E0H             ;18D6   28 08         (
CP E                   ;18D8   BB            »
INC HL                 ;18D9   23            #
JR Z,18E0H             ;18DA   28 04         (
INC BC                 ;18DC   03            
JR 18D4H               ;18DD   18 F5         õ
PUSH HL                ;18DF   E5            å
EX (SP),HL             ;18E0   E3            ã
EX DE,HL               ;18E1   EB            ë
LD HL,(4642H)          ;18E2   2A 42 46      *BF
XOR A                  ;18E5   AF            ¯
PUSH AF                ;18E6   F5            õ
LD A,(HL)              ;18E7   7E            ~
OR A                   ;18E8   B7            ·
JR Z,18F2H             ;18E9   28 07         (
CALL 1633H             ;18EB   CD 33 16      Í3
POP AF                 ;18EE   F1            ñ
INC A                  ;18EF   3C            <
JR 18E6H               ;18F0   18 F4         ô
EX DE,HL               ;18F2   EB            ë
INC BC                 ;18F3   03            
CALL 1796H             ;18F4   CD 96 17      Í
PUSH HL                ;18F7   E5            å
LD HL,(4644H)          ;18F8   2A 44 46      *DF
ADD HL,BC              ;18FB   09            	
LD (4644H),HL          ;18FC   22 44 46      "DF
POP HL                 ;18FF   E1            á
EX DE,HL               ;1900   EB            ë
DEC BC                 ;1901   0B            

ADD HL,BC              ;1902   09            	
LD (HL),0DH            ;1903   36 0D         6
POP AF                 ;1905   F1            ñ
LD E,A                 ;1906   5F            _
LD D,01H               ;1907   16 01         
POP HL                 ;1909   E1            á
JP 162DH               ;190A   C3 2D 16      Ã-
CALL 162DH             ;190D   CD 2D 16      Í-
CP 0DH                 ;1910   FE 0D         þ
JP Z,1670H             ;1912   CA 70 16      Êp
PUSH HL                ;1915   E5            å
DEC HL                 ;1916   2B            +
INC HL                 ;1917   23            #
CALL 162DH             ;1918   CD 2D 16      Í-
CP 2BH                 ;191B   FE 2B         þ+
JR NZ,1921H            ;191D   20 02          
LD A,BCH               ;191F   3E BC         >¼
CP 2DH                 ;1921   FE 2D         þ-
JR NZ,1927H            ;1923   20 02          
LD A,BDH               ;1925   3E BD         >½
LD (HL),A              ;1927   77            w
CALL 193DH             ;1928   CD 3D 19      Í=
JR Z,1917H             ;192B   28 EA         (ê
CP 45H                 ;192D   FE 45         þE
JR Z,1917H             ;192F   28 E6         (æ
CP 0DH                 ;1931   FE 0D         þ
JP NZ,166FH            ;1933   C2 6F 16      Âo
POP HL                 ;1936   E1            á
CALL 22AFH             ;1937   CD AF 22      Í¯"
JP 167AH               ;193A   C3 7A 16      Ãz
CALL 1659H             ;193D   CD 59 16      ÍY
JR NC,1944H            ;1940   30 02         0
CP (HL)                ;1942   BE            ¾
RET                    ;1943   C9            É
CP 2EH                 ;1944   FE 2E         þ.
RET Z                  ;1946   C8            È
CP BDH                 ;1947   FE BD         þ½
RET Z                  ;1949   C8            È
CP BCH                 ;194A   FE BC         þ¼
RET                    ;194C   C9            É
PUSH HL                ;194D   E5            å
LD HL,(4644H)          ;194E   2A 44 46      *DF
LD DE,0000H            ;1951   11 00 00      
LD A,(HL)              ;1954   7E            ~
OR A                   ;1955   B7            ·
JP P,1398H             ;1956   F2 98 13      ò
CP C1H                 ;1959   FE C1         þÁ
JP C,1974H             ;195B   DA 74 19      Út
SUB D1H                ;195E   D6 D1         ÖÑ
JP NC,1398H            ;1960   D2 98 13      Ò
LD E,03H               ;1963   1E 03         

ADD HL,DE              ;1965   19            
LD E,(HL)              ;1966   5E            ^
INC HL                 ;1967   23            #
LD D,(HL)              ;1968   56            V
JP 1970H               ;1969   C3 70 19      Ãp
SRL D                  ;196C   CB 3A         Ë:
RR E                   ;196E   CB 1B         Ë
INC A                  ;1970   3C            <
JP NZ,196CH            ;1971   C2 6C 19      Âl
POP HL                 ;1974   E1            á
RET                    ;1975   C9            É
LD HL,456CH            ;1976   21 6C 45      !lE
JR 197EH               ;1979   18 03         
LD HL,4570H            ;197B   21 70 45      !pE
LD (HL),C              ;197E   71            q
INC HL                 ;197F   23            #
LD (HL),B              ;1980   70            p
INC HL                 ;1981   23            #
LD (HL),E              ;1982   73            s
INC HL                 ;1983   23            #
LD (HL),D              ;1984   72            r
INC HL                 ;1985   23            #
RET                    ;1986   C9            É
XOR A                  ;1987   AF            ¯
LD (4577H),A           ;1988   32 77 45      2wE
RET                    ;198B   C9            É
EXX                    ;198C   D9            Ù
LD BC,0005H            ;198D   01 05 00      
CALL 19A0H             ;1990   CD A0 19      Í 
CALL 22AFH             ;1993   CD AF 22      Í¯"
CALL 1814H             ;1996   CD 14 18      Í
CALL 194DH             ;1999   CD 4D 19      ÍM
EXX                    ;199C   D9            Ù
LD BC,FFFBH            ;199D   01 FB FF      ûÿ
LD HL,(4644H)          ;19A0   2A 44 46      *DF
ADD HL,BC              ;19A3   09            	
LD (4644H),HL          ;19A4   22 44 46      "DF
EXX                    ;19A7   D9            Ù
RET                    ;19A8   C9            É
CALL 198CH             ;19A9   CD 8C 19      Í
LD A,D                 ;19AC   7A            z
OR A                   ;19AD   B7            ·
RET Z                  ;19AE   C8            È
JP 1398H               ;19AF   C3 98 13      Ã
LD HL,(4801H)          ;19B2   2A 01 48      *H
CALL 162DH             ;19B5   CD 2D 16      Í-
CP 0DH                 ;19B8   FE 0D         þ
JP Z,19C7H             ;19BA   CA C7 19      ÊÇ
CALL 169AH             ;19BD   CD 9A 16      Í
LD A,(0122H)           ;19C0   3A 22 01      :"
LD C,B                 ;19C3   48            H
JP 19E1H               ;19C4   C3 E1 19      Ãá
LD HL,(47FDH)          ;19C7   2A FD 47      *ýG
XOR A                  ;19CA   AF            ¯
OR H                   ;19CB   B4            ´
JP Z,124BH             ;19CC   CA 4B 12      ÊK
LD DE,47FDH            ;19CF   11 FD 47      ýG
LD BC,0004H            ;19D2   01 04 00      
LDIR                   ;19D5   ED B0         í°
LD (4801H),HL          ;19D7   22 01 48      "H
LD A,(47FEH)           ;19DA   3A FE 47      :þG
OR A                   ;19DD   B7            ·
JP Z,1B2DH             ;19DE   CA 2D 1B      Ê-
LD HL,E000H            ;19E1   21 00 E0      !à
LD (HL),F8H            ;19E4   36 F8         6ø
INC HL                 ;19E6   23            #
LD A,(HL)              ;19E7   7E            ~
INC A                  ;19E8   3C            <
JP Z,19F7H             ;19E9   CA F7 19      Ê÷
CALL 001EH             ;19EC   CD 1E 00      Í

JR NZ,19F7H            ;19EF   20 06          
CALL 13C8H             ;19F1   CD C8 13      ÍÈ
JP 1385H               ;19F4   C3 85 13      Ã

LD HL,(4642H)          ;19F7   2A 42 46      *BF
XOR A                  ;19FA   AF            ¯
LD (HL),A              ;19FB   77            w
INC HL                 ;19FC   23            #
LD (HL),A              ;19FD   77            w
INC HL                 ;19FE   23            #
LD (4644H),HL          ;19FF   22 44 46      "DF
LD HL,(4801H)          ;1A02   2A 01 48      *H
LD A,(HL)              ;1A05   7E            ~
OR A                   ;1A06   B7            ·
JP P,1B3FH             ;1A07   F2 3F 1B      ò?
CP AAH                 ;1A0A   FE AA         þª
JP NC,138EH            ;1A0C   D2 8E 13      Ò
LD DE,1A1FH            ;1A0F   11 1F 1A      
INC HL                 ;1A12   23            #
EX DE,HL               ;1A13   EB            ë
ADD A,A                ;1A14   87            
LD C,A                 ;1A15   4F            O
LD B,00H               ;1A16   06 00         
ADD HL,BC              ;1A18   09            	
LD C,(HL)              ;1A19   4E            N
INC HL                 ;1A1A   23            #
LD B,(HL)              ;1A1B   46            F
EX DE,HL               ;1A1C   EB            ë
PUSH BC                ;1A1D   C5            Å
RET                    ;1A1E   C9            É
DAA                    ;1A1F   27            '
DEC DE                 ;1A20   1B            
DAA                    ;1A21   27            '
DEC DE                 ;1A22   1B            
HALT                   ;1A23   76            v
LD A,(DE)              ;1A24   1A            
RR H                   ;1A25   CB 1C         Ë

LD L,A                 ;1A27   6F            o
LD A,(DE)              ;1A28   1A            
CPL                    ;1A29   2F            /
INC E                  ;1A2A   1C            

CCF                    ;1A2B   3F            ?
DEC DE                 ;1A2C   1B            
LD E,H                 ;1A2D   5C            \
DEC E                  ;1A2E   1D            

ADD A,D                ;1A2F   82            
LD HL,1CDBH            ;1A30   21 DB 1C      !Û

XOR A                  ;1A33   AF            ¯
RRA                    ;1A34   1F            
OR 1CH                 ;1A35   F6 1C         ö

LD HL,(F41DH)          ;1A37   2A 1D F4      *
ô
DEC E                  ;1A3A   1D            

LD (HL),1BH            ;1A3B   36 1B         6
DEC L                  ;1A3D   2D            -
DEC DE                 ;1A3E   1B            
OR 1FH                 ;1A3F   F6 1F         ö
LD (HL),2AH            ;1A41   36 2A         6*
CP E                   ;1A43   BB            »
ADD HL,HL              ;1A44   29            )
ADC A,A                ;1A45   8F            
ADD HL,HL              ;1A46   29            )
LD H,(HL)              ;1A47   66            f
LD HL,2050H            ;1A48   21 50 20      !P 
OR B                   ;1A4B   B0            °
LD HL,1E7CH            ;1A4C   21 7C 1E      !|

INC H                  ;1A4F   24            $
DEC DE                 ;1A50   1B            
LD (HL),A              ;1A51   77            w
LD HL,2226H            ;1A52   21 26 22      !&"
LD B,(HL)              ;1A55   46            F
LD (28B2H),HL          ;1A56   22 B2 28      "²(
AND A                  ;1A59   A7            
DEC HL                 ;1A5A   2B            +
RST 10H                ;1A5B   D7            ×
DEC HL                 ;1A5C   2B            +
DEC B                  ;1A5D   05            
INC L                  ;1A5E   2C            ,
LD D,H                 ;1A5F   54            T
JR Z,1A24H             ;1A60   28 C2         (Â
JR Z,1A60H             ;1A62   28 FC         (ü
JR Z,1A90H             ;1A64   28 2A         (*
ADD HL,HL              ;1A66   29            )
LD L,29H               ;1A67   2E 29         .)
LD D,A                 ;1A69   57            W
JR Z,1A44H             ;1A6A   28 D8         (Ø
INC L                  ;1A6C   2C            ,
LD L,2DH               ;1A6D   2E 2D         .-
CALL 1832H             ;1A6F   CD 32 18      Í2
JP 124BH               ;1A72   C3 4B 12      ÃK
NOP                    ;1A75   00            
LD A,(29B8H)           ;1A76   3A B8 29      :¸)
OR A                   ;1A79   B7            ·
JP NZ,124BH            ;1A7A   C2 4B 12      ÂK
LD B,A                 ;1A7D   47            G
CALL 168BH             ;1A7E   CD 8B 16      Í
CP A                   ;1A81   BF            ¿
ADC A,H                ;1A82   8C            
LD A,(DE)              ;1A83   1A            
CALL 169AH             ;1A84   CD 9A 16      Í
LD D,B                 ;1A87   50            P
CALL 3C75H             ;1A88   CD 75 3C      Íu<
INC B                  ;1A8B   04            
LD A,B                 ;1A8C   78            x
LD (1A75H),A           ;1A8D   32 75 1A      2u
PUSH HL                ;1A90   E5            å
CALL 1B08H             ;1A91   CD 08 1B      Í
LD HL,457EH            ;1A94   21 7E 45      !~E
CALL 1896H             ;1A97   CD 96 18      Í
DEC A                  ;1A9A   3D            =
CALL 1897H             ;1A9B   CD 97 18      Í
POP HL                 ;1A9E   E1            á
CALL 168BH             ;1A9F   CD 8B 16      Í
DEC C                  ;1AA2   0D            
PUSH HL                ;1AA3   E5            å
LD A,(DE)              ;1AA4   1A            
LD HL,4806H            ;1AA5   21 06 48      !H
PUSH HL                ;1AA8   E5            å
CALL 175AH             ;1AA9   CD 5A 17      ÍZ
POP HL                 ;1AAC   E1            á
JP Z,124BH             ;1AAD   CA 4B 12      ÊK
CALL 17E8H             ;1AB0   CD E8 17      Íè
LD DE,4455H            ;1AB3   11 55 44      UD
CALL 1799H             ;1AB6   CD 99 17      Í
LD HL,(457EH)          ;1AB9   2A 7E 45      *~E
EX DE,HL               ;1ABC   EB            ë
LD HL,(4457H)          ;1ABD   2A 57 44      *WD
CALL 1662H             ;1AC0   CD 62 16      Íb
JP C,1ADFH             ;1AC3   DA DF 1A      Úß
EX DE,HL               ;1AC6   EB            ë
LD HL,(4580H)          ;1AC7   2A 80 45      *E
CALL 1662H             ;1ACA   CD 62 16      Íb
JP C,1ADFH             ;1ACD   DA DF 1A      Úß
CALL 1443H             ;1AD0   CD 43 14      ÍC
LD DE,4400H            ;1AD3   11 00 44      D
CALL 1B12H             ;1AD6   CD 12 1B      Í
CALL 001EH             ;1AD9   CD 1E 00      Í

JP Z,124BH             ;1ADC   CA 4B 12      ÊK
LD HL,(4455H)          ;1ADF   2A 55 44      *UD
JP 1AA8H               ;1AE2   C3 A8 1A      Ã¨
CALL 16F1H             ;1AE5   CD F1 16      Íñ
LD (457EH),DE          ;1AE8   ED 53 7E 45   íS~E
CALL 168BH             ;1AEC   CD 8B 16      Í
DEC C                  ;1AEF   0D            
LD SP,HL               ;1AF0   F9            ù
LD A,(DE)              ;1AF1   1A            
EX DE,HL               ;1AF2   EB            ë
LD (4580H),HL          ;1AF3   22 80 45      "E
JP 1AA5H               ;1AF6   C3 A5 1A      Ã¥
CALL 169AH             ;1AF9   CD 9A 16      Í
CP L                   ;1AFC   BD            ½
CP 0DH                 ;1AFD   FE 0D         þ
JP Z,1AA5H             ;1AFF   CA A5 1A      Ê¥
CALL 16F1H             ;1B02   CD F1 16      Íñ
JP 1AF2H               ;1B05   C3 F2 1A      Ãò
LD A,(1A75H)           ;1B08   3A 75 1A      :u
OR A                   ;1B0B   B7            ·
JP Z,0009H             ;1B0C   CA 09 00      Ê	
JP 3BA1H               ;1B0F   C3 A1 3B      Ã¡;
LD A,(1A75H)           ;1B12   3A 75 1A      :u
OR A                   ;1B15   B7            ·
JR NZ,1B1EH            ;1B16   20 06          
CALL 0018H             ;1B18   CD 18 00      Í
JP 0009H               ;1B1B   C3 09 00      Ã	
CALL 3C05H             ;1B1E   CD 05 3C      Í<
JP 3BA1H               ;1B21   C3 A1 3B      Ã¡;
CALL 1987H             ;1B24   CD 87 19      Í
CALL 163DH             ;1B27   CD 3D 16      Í=
JP 19B8H               ;1B2A   C3 B8 19      Ã¸
CALL 13C4H             ;1B2D   CD C4 13      ÍÄ
LD (4801H),HL          ;1B30   22 01 48      "H
JP 124BH               ;1B33   C3 4B 12      ÃK
CALL 13C4H             ;1B36   CD C4 13      ÍÄ
LD (4801H),HL          ;1B39   22 01 48      "H
JP 1385H               ;1B3C   C3 85 13      Ã

PUSH HL                ;1B3F   E5            å
CALL 1829H             ;1B40   CD 29 18      Í)
JP Z,138EH             ;1B43   CA 8E 13      Ê
CP B6H                 ;1B46   FE B6         þ¶
INC HL                 ;1B48   23            #
JR NZ,1B40H            ;1B49   20 F5          õ
CALL 22AFH             ;1B4B   CD AF 22      Í¯"
LD (4801H),HL          ;1B4E   22 01 48      "H
CALL 1976H             ;1B51   CD 76 19      Ív
POP HL                 ;1B54   E1            á
CALL 2613H             ;1B55   CD 13 26      Í&
CALL 2436H             ;1B58   CD 36 24      Í6$
CALL 169AH             ;1B5B   CD 9A 16      Í
OR (HL)                ;1B5E   B6            ¶
CALL 197BH             ;1B5F   CD 7B 19      Í{
CALL 1B6AH             ;1B62   CD 6A 1B      Íj
SBC A,L                ;1B65   9D            
INC DE                 ;1B66   13            
JP 19B2H               ;1B67   C3 B2 19      Ã²
LD HL,456FH            ;1B6A   21 6F 45      !oE
LD B,(HL)              ;1B6D   46            F
INC HL                 ;1B6E   23            #
LD C,(HL)              ;1B6F   4E            N
INC HL                 ;1B70   23            #
LD A,(HL)              ;1B71   7E            ~
LD DE,(4572H)          ;1B72   ED 5B 72 45   í[rE
OR A                   ;1B76   B7            ·
JP NZ,1B84H            ;1B77   C2 84 1B      Â
OR B                   ;1B7A   B0            °
JP NZ,1670H            ;1B7B   C2 70 16      Âp
CALL 1824H             ;1B7E   CD 24 18      Í$
JP 167AH               ;1B81   C3 7A 16      Ãz
XOR A                  ;1B84   AF            ¯
OR B                   ;1B85   B0            °
JP Z,1670H             ;1B86   CA 70 16      Êp
LD HL,4559H            ;1B89   21 59 45      !YE
XOR A                  ;1B8C   AF            ¯
LD B,A                 ;1B8D   47            G
SBC HL,DE              ;1B8E   ED 52         íR
JP Z,1BC0H             ;1B90   CA C0 1B      ÊÀ
LD HL,(456CH)          ;1B93   2A 6C 45      *lE
PUSH HL                ;1B96   E5            å
XOR A                  ;1B97   AF            ¯
SBC HL,BC              ;1B98   ED 42         íB
LD B,H                 ;1B9A   44            D
LD C,L                 ;1B9B   4D            M
JR C,1BA3H             ;1B9C   38 05         8
CALL 177CH             ;1B9E   CD 7C 17      Í|
JR 1BABH               ;1BA1   18 08         
PUSH BC                ;1BA3   C5            Å
CALL 1651H             ;1BA4   CD 51 16      ÍQ
CALL 1766H             ;1BA7   CD 66 17      Íf
POP BC                 ;1BAA   C1            Á
CALL 189CH             ;1BAB   CD 9C 18      Í
LD HL,(456EH)          ;1BAE   2A 6E 45      *nE
EX DE,HL               ;1BB1   EB            ë
CALL 1801H             ;1BB2   CD 01 18      Í
EX DE,HL               ;1BB5   EB            ë
POP BC                 ;1BB6   C1            Á
LD A,C                 ;1BB7   79            y
OR A                   ;1BB8   B7            ·
JR Z,1BBDH             ;1BB9   28 02         (
LDIR                   ;1BBB   ED B0         í°
JP 167AH               ;1BBD   C3 7A 16      Ãz
LD HL,(456EH)          ;1BC0   2A 6E 45      *nE
EX DE,HL               ;1BC3   EB            ë
CALL 1801H             ;1BC4   CD 01 18      Í
EX DE,HL               ;1BC7   EB            ë
LD DE,4559H            ;1BC8   11 59 45      YE
PUSH DE                ;1BCB   D5            Õ
LD B,03H               ;1BCC   06 03         
LD C,02H               ;1BCE   0E 02         
CALL 1659H             ;1BD0   CD 59 16      ÍY
JP NC,1398H            ;1BD3   D2 98 13      Ò
LD (DE),A              ;1BD6   12            
INC DE                 ;1BD7   13            
INC HL                 ;1BD8   23            #
DEC C                  ;1BD9   0D            
JR NZ,1BD0H            ;1BDA   20 F4          ô
LD A,0DH               ;1BDC   3E 0D         >
LD (DE),A              ;1BDE   12            
INC DE                 ;1BDF   13            
DEC B                  ;1BE0   05            
JR NZ,1BCEH            ;1BE1   20 EB          ë
CALL 168BH             ;1BE3   CD 8B 16      Í
DEC C                  ;1BE6   0D            
SBC A,B                ;1BE7   98            
INC DE                 ;1BE8   13            
POP HL                 ;1BE9   E1            á
CALL 198CH             ;1BEA   CD 8C 19      Í
LD B,00H               ;1BED   06 00         
LD A,E                 ;1BEF   7B            {
CP 18H                 ;1BF0   FE 18         þ
JP NC,1398H            ;1BF2   D2 98 13      Ò
SUB 0CH                ;1BF5   D6 0C         Ö

JR C,1BFBH             ;1BF7   38 02         8
LD E,A                 ;1BF9   5F            _
INC B                  ;1BFA   04            
LD A,B                 ;1BFB   78            x
PUSH AF                ;1BFC   F5            õ
PUSH HL                ;1BFD   E5            å
LD HL,0E10H            ;1BFE   21 10 0E      !
CALL 16C8H             ;1C01   CD C8 16      ÍÈ
POP HL                 ;1C04   E1            á
PUSH DE                ;1C05   D5            Õ
INC HL                 ;1C06   23            #
CALL 198CH             ;1C07   CD 8C 19      Í
LD A,E                 ;1C0A   7B            {
CP 3CH                 ;1C0B   FE 3C         þ<
JP NC,1398H            ;1C0D   D2 98 13      Ò
PUSH HL                ;1C10   E5            å
LD HL,003CH            ;1C11   21 3C 00      !<
CALL 16C8H             ;1C14   CD C8 16      ÍÈ
POP HL                 ;1C17   E1            á
EX (SP),HL             ;1C18   E3            ã
ADD HL,DE              ;1C19   19            
EX (SP),HL             ;1C1A   E3            ã
INC HL                 ;1C1B   23            #
CALL 198CH             ;1C1C   CD 8C 19      Í
LD A,E                 ;1C1F   7B            {
CP 3CH                 ;1C20   FE 3C         þ<
JP NC,1398H            ;1C22   D2 98 13      Ò
POP HL                 ;1C25   E1            á
ADD HL,DE              ;1C26   19            
EX DE,HL               ;1C27   EB            ë
POP AF                 ;1C28   F1            ñ
CALL 0033H             ;1C29   CD 33 00      Í3
JP 167AH               ;1C2C   C3 7A 16      Ãz
LD B,00H               ;1C2F   06 00         
CALL 168BH             ;1C31   CD 8B 16      Í
CP A                   ;1C34   BF            ¿
LD B,L                 ;1C35   45            E
INC E                  ;1C36   1C            

INC HL                 ;1C37   23            #
INC B                  ;1C38   04            
CP 54H                 ;1C39   FE 54         þT
JP Z,1C45H             ;1C3B   CA 45 1C      ÊE

CP 50H                 ;1C3E   FE 50         þP
JP NZ,138EH            ;1C40   C2 8E 13      Â
LD B,80H               ;1C43   06 80         
LD A,B                 ;1C45   78            x
LD (457DH),A           ;1C46   32 7D 45      2}E
CALL 1829H             ;1C49   CD 29 18      Í)
JP NZ,1C60H            ;1C4C   C2 60 1C      Â`

LD A,(457DH)           ;1C4F   3A 7D 45      :}E
LD BC,19B5H            ;1C52   01 B5 19      µ
PUSH BC                ;1C55   C5            Å
CP 01H                 ;1C56   FE 01         þ
RET Z                  ;1C58   C8            È
OR A                   ;1C59   B7            ·
JP Z,0006H             ;1C5A   CA 06 00      Ê
JP 3BA6H               ;1C5D   C3 A6 3B      Ã¦;
CALL 168BH             ;1C60   CD 8B 16      Í
DEC SP                 ;1C63   3B            ;
LD H,(HL)              ;1C64   66            f
INC E                  ;1C65   1C            

CALL 168BH             ;1C66   CD 8B 16      Í
INC L                  ;1C69   2C            ,
LD A,L                 ;1C6A   7D            }
INC E                  ;1C6B   1C            

LD A,(457DH)           ;1C6C   3A 7D 45      :}E
LD BC,1C7DH            ;1C6F   01 7D 1C      }

PUSH BC                ;1C72   C5            Å
CP 01H                 ;1C73   FE 01         þ
RET Z                  ;1C75   C8            È
OR A                   ;1C76   B7            ·
JP Z,000FH             ;1C77   CA 0F 00      Ê
JP 3C4AH               ;1C7A   C3 4A 3C      ÃJ<
CALL 1829H             ;1C7D   CD 29 18      Í)
JP Z,19B5H             ;1C80   CA B5 19      Êµ
CP 3BH                 ;1C83   FE 3B         þ;
JR Z,1C89H             ;1C85   28 02         (
CP 2CH                 ;1C87   FE 2C         þ,
JP Z,1C60H             ;1C89   CA 60 1C      Ê`

CALL 22AFH             ;1C8C   CD AF 22      Í¯"
PUSH HL                ;1C8F   E5            å
LD A,D                 ;1C90   7A            z
OR A                   ;1C91   B7            ·
JP NZ,1CC5H            ;1C92   C2 C5 1C      ÂÅ

LD HL,(4644H)          ;1C95   2A 44 46      *DF
LD DE,4400H            ;1C98   11 00 44      D
PUSH DE                ;1C9B   D5            Õ
CALL 322DH             ;1C9C   CD 2D 32      Í-2
POP DE                 ;1C9F   D1            Ñ
LD A,(457DH)           ;1CA0   3A 7D 45      :}E
LD BC,1CB3H            ;1CA3   01 B3 1C      ³

PUSH BC                ;1CA6   C5            Å
CP 01H                 ;1CA7   FE 01         þ
JP Z,2C4EH             ;1CA9   CA 4E 2C      ÊN,
OR A                   ;1CAC   B7            ·
JP Z,3D17H             ;1CAD   CA 17 3D      Ê=
JP 3BB6H               ;1CB0   C3 B6 3B      Ã¶;
POP HL                 ;1CB3   E1            á
CALL 1829H             ;1CB4   CD 29 18      Í)
JR Z,1CBFH             ;1CB7   28 06         (
CP 3BH                 ;1CB9   FE 3B         þ;
JR Z,1CBFH             ;1CBB   28 02         (
CP 2CH                 ;1CBD   FE 2C         þ,
JP Z,1C49H             ;1CBF   CA 49 1C      ÊI

JP 138EH               ;1CC2   C3 8E 13      Ã
CALL 1801H             ;1CC5   CD 01 18      Í
JP 1CA0H               ;1CC8   C3 A0 1C      Ã 

CALL 1987H             ;1CCB   CD 87 19      Í
XOR A                  ;1CCE   AF            ¯
LD (457AH),A           ;1CCF   32 7A 45      2zE
LD (4565H),A           ;1CD2   32 65 45      2eE
CALL 1659H             ;1CD5   CD 59 16      ÍY
JP NC,1CEAH            ;1CD8   D2 EA 1C      Òê

CALL 16F1H             ;1CDB   CD F1 16      Íñ
EX DE,HL               ;1CDE   EB            ë
CALL 17A5H             ;1CDF   CD A5 17      Í¥
ADC A,(HL)             ;1CE2   8E            
INC DE                 ;1CE3   13            
JP NZ,138EH            ;1CE4   C2 8E 13      Â
JP 19CFH               ;1CE7   C3 CF 19      ÃÏ
CALL 1857H             ;1CEA   CD 57 18      ÍW
CALL 187CH             ;1CED   CD 7C 18      Í|
LD HL,4806H            ;1CF0   21 06 48      !H
JP 19CFH               ;1CF3   C3 CF 19      ÃÏ
CALL 16F1H             ;1CF6   CD F1 16      Íñ
LD (4801H),HL          ;1CF9   22 01 48      "H
EX DE,HL               ;1CFC   EB            ë
CALL 17A5H             ;1CFD   CD A5 17      Í¥
ADC A,(HL)             ;1D00   8E            
INC DE                 ;1D01   13            
JP NZ,138EH            ;1D02   C2 8E 13      Â
EXX                    ;1D05   D9            Ù
LD HL,4805H            ;1D06   21 05 48      !H
LD A,(HL)              ;1D09   7E            ~
CP 0FH                 ;1D0A   FE 0F         þ
JP Z,13A7H             ;1D0C   CA A7 13      Ê
INC (HL)               ;1D0F   34            4
DEC HL                 ;1D10   2B            +
DEC HL                 ;1D11   2B            +
LD DE,(464AH)          ;1D12   ED 5B 4A 46   í[JF
DEC DE                 ;1D16   1B            
LD BC,0007H            ;1D17   01 07 00      
LDDR                   ;1D1A   ED B8         í¸
INC DE                 ;1D1C   13            
LD (464AH),DE          ;1D1D   ED 53 4A 46   íSJF
LD C,07H               ;1D21   0E 07         
ADD HL,BC              ;1D23   09            	
LD (HL),00H            ;1D24   36 00         6
EXX                    ;1D26   D9            Ù
JP 19CFH               ;1D27   C3 CF 19      ÃÏ
LD HL,4805H            ;1D2A   21 05 48      !H
XOR A                  ;1D2D   AF            ¯
CP (HL)                ;1D2E   BE            ¾
JP Z,138EH             ;1D2F   CA 8E 13      Ê
DEC (HL)               ;1D32   35            5
LD HL,4803H            ;1D33   21 03 48      !H
LD A,(HL)              ;1D36   7E            ~
OR A                   ;1D37   B7            ·
JP Z,1D4BH             ;1D38   CA 4B 1D      ÊK

DEC (HL)               ;1D3B   35            5
INC HL                 ;1D3C   23            #
DEC (HL)               ;1D3D   35            5
LD HL,(4648H)          ;1D3E   2A 48 46      *HF
LD BC,0013H            ;1D41   01 13 00      
ADD HL,BC              ;1D44   09            	
LD (4648H),HL          ;1D45   22 48 46      "HF
JP 1D33H               ;1D48   C3 33 1D      Ã3

LD HL,(464AH)          ;1D4B   2A 4A 46      *JF
LD DE,47FDH            ;1D4E   11 FD 47      ýG
LD BC,0007H            ;1D51   01 07 00      
LDIR                   ;1D54   ED B0         í°
LD (464AH),HL          ;1D56   22 4A 46      "JF
JP 19B2H               ;1D59   C3 B2 19      Ã²
CALL 2613H             ;1D5C   CD 13 26      Í&
CALL 169AH             ;1D5F   CD 9A 16      Í
OR (HL)                ;1D62   B6            ¶
PUSH DE                ;1D63   D5            Õ
CALL 1DEBH             ;1D64   CD EB 1D      Íë

POP HL                 ;1D67   E1            á
LD (47F0H),HL          ;1D68   22 F0 47      "ðG
EX DE,HL               ;1D6B   EB            ë
CALL 2441H             ;1D6C   CD 41 24      ÍA$
CALL 1824H             ;1D6F   CD 24 18      Í$
CALL 1697H             ;1D72   CD 97 16      Í
XOR (HL)               ;1D75   AE            ®
CALL 1DEBH             ;1D76   CD EB 1D      Íë

LD DE,47F8H            ;1D79   11 F8 47      øG
CALL 1824H             ;1D7C   CD 24 18      Í$
CALL 1688H             ;1D7F   CD 88 16      Í
XOR A                  ;1D82   AF            ¯
ADC A,L                ;1D83   8D            
DEC E                  ;1D84   1D            

CALL 1DEBH             ;1D85   CD EB 1D      Íë

LD HL,(4644H)          ;1D88   2A 44 46      *DF
JR 1D90H               ;1D8B   18 03         
LD HL,1614H            ;1D8D   21 14 16      !
LD DE,47F2H            ;1D90   11 F2 47      òG
LD A,(HL)              ;1D93   7E            ~
LD (47F7H),A           ;1D94   32 F7 47      2÷G
LD BC,0005H            ;1D97   01 05 00      
LDIR                   ;1D9A   ED B0         í°
LD HL,(4648H)          ;1D9C   2A 48 46      *HF
LD DE,(47F0H)          ;1D9F   ED 5B F0 47   í[ðG
LD A,(4803H)           ;1DA3   3A 03 48      :H
INC A                  ;1DA6   3C            <
DEC A                  ;1DA7   3D            =
JP Z,1DCCH             ;1DA8   CA CC 1D      ÊÌ

EX AF,AF'              ;1DAB   08            
LD A,(HL)              ;1DAC   7E            ~
SUB E                  ;1DAD   93            
LD B,A                 ;1DAE   47            G
INC HL                 ;1DAF   23            #
LD A,(HL)              ;1DB0   7E            ~
SUB D                  ;1DB1   92            
OR B                   ;1DB2   B0            °
LD BC,0012H            ;1DB3   01 12 00      
ADD HL,BC              ;1DB6   09            	
JP Z,1DBEH             ;1DB7   CA BE 1D      Ê¾

EX AF,AF'              ;1DBA   08            
JP 1DA7H               ;1DBB   C3 A7 1D      Ã

LD (4648H),HL          ;1DBE   22 48 46      "HF
EX AF,AF'              ;1DC1   08            
DEC A                  ;1DC2   3D            =
LD HL,4803H            ;1DC3   21 03 48      !H
LD B,(HL)              ;1DC6   46            F
LD (HL),A              ;1DC7   77            w
SUB B                  ;1DC8   90            
INC HL                 ;1DC9   23            #
ADD A,(HL)             ;1DCA   86            
LD (HL),A              ;1DCB   77            w
LD HL,4804H            ;1DCC   21 04 48      !H
LD A,(HL)              ;1DCF   7E            ~
CP 0FH                 ;1DD0   FE 0F         þ
JP Z,13A2H             ;1DD2   CA A2 13      Ê¢
INC (HL)               ;1DD5   34            4
DEC HL                 ;1DD6   2B            +
INC (HL)               ;1DD7   34            4
DEC HL                 ;1DD8   2B            +
LD DE,(4648H)          ;1DD9   ED 5B 48 46   í[HF
LD BC,0013H            ;1DDD   01 13 00      
DEC DE                 ;1DE0   1B            
LDDR                   ;1DE1   ED B8         í¸
INC DE                 ;1DE3   13            
EX DE,HL               ;1DE4   EB            ë
LD (4648H),HL          ;1DE5   22 48 46      "HF
JP 19B2H               ;1DE8   C3 B2 19      Ã²
CALL 22AFH             ;1DEB   CD AF 22      Í¯"
LD (4801H),HL          ;1DEE   22 01 48      "H
JP 1814H               ;1DF1   C3 14 18      Ã
LD A,(4803H)           ;1DF4   3A 03 48      :H
OR A                   ;1DF7   B7            ·
JP Z,138EH             ;1DF8   CA 8E 13      Ê
CALL 25CDH             ;1DFB   CD CD 25      ÍÍ%
LD (4801H),HL          ;1DFE   22 01 48      "H
LD HL,(4648H)          ;1E01   2A 48 46      *HF
CALL NC,1E77H          ;1E04   D4 77 1E      Ôw

LD A,E                 ;1E07   7B            {
SUB (HL)               ;1E08   96            
INC HL                 ;1E09   23            #
LD B,A                 ;1E0A   47            G
LD A,D                 ;1E0B   7A            z
SUB (HL)               ;1E0C   96            
OR B                   ;1E0D   B0            °
JP Z,1E28H             ;1E0E   CA 28 1E      Ê(

EXX                    ;1E11   D9            Ù
LD HL,4803H            ;1E12   21 03 48      !H
LD A,(HL)              ;1E15   7E            ~
DEC A                  ;1E16   3D            =
JP Z,138EH             ;1E17   CA 8E 13      Ê
LD (HL),A              ;1E1A   77            w
INC HL                 ;1E1B   23            #
DEC (HL)               ;1E1C   35            5
EXX                    ;1E1D   D9            Ù
LD BC,0012H            ;1E1E   01 12 00      
ADD HL,BC              ;1E21   09            	
LD (4648H),HL          ;1E22   22 48 46      "HF
JP 1E07H               ;1E25   C3 07 1E      Ã

INC HL                 ;1E28   23            #
CALL 2441H             ;1E29   CD 41 24      ÍA$
PUSH DE                ;1E2C   D5            Õ
PUSH HL                ;1E2D   E5            å
CALL 2D4DH             ;1E2E   CD 4D 2D      ÍM-
POP HL                 ;1E31   E1            á
POP DE                 ;1E32   D1            Ñ
LD BC,0005H            ;1E33   01 05 00      
ADD HL,BC              ;1E36   09            	
LD A,(HL)              ;1E37   7E            ~
INC HL                 ;1E38   23            #
PUSH HL                ;1E39   E5            å
OR A                   ;1E3A   B7            ·
JP P,1E57H             ;1E3B   F2 57 1E      òW

EX DE,HL               ;1E3E   EB            ë
CALL 33EEH             ;1E3F   CD EE 33      Íî3
POP HL                 ;1E42   E1            á
LD BC,0005H            ;1E43   01 05 00      
JP C,1E62H             ;1E46   DA 62 1E      Úb

ADD HL,BC              ;1E49   09            	
LD DE,47FDH            ;1E4A   11 FD 47      ýG
INC C                  ;1E4D   0C            

LDIR                   ;1E4E   ED B0         í°
LD HL,(4801H)          ;1E50   2A 01 48      *H
LD A,(HL)              ;1E53   7E            ~
JP 19B8H               ;1E54   C3 B8 19      Ã¸
CALL 33EEH             ;1E57   CD EE 33      Íî3
POP HL                 ;1E5A   E1            á
LD BC,0005H            ;1E5B   01 05 00      
CCF                    ;1E5E   3F            ?
JP C,1E49H             ;1E5F   DA 49 1E      ÚI

LD C,0BH               ;1E62   0E 0B         

ADD HL,BC              ;1E64   09            	
LD (4648H),HL          ;1E65   22 48 46      "HF
LD HL,4803H            ;1E68   21 03 48      !H
DEC (HL)               ;1E6B   35            5
INC HL                 ;1E6C   23            #
DEC (HL)               ;1E6D   35            5
CALL 1688H             ;1E6E   CD 88 16      Í
INC L                  ;1E71   2C            ,
OR D                   ;1E72   B2            ²
ADD HL,DE              ;1E73   19            
JP 1DF4H               ;1E74   C3 F4 1D      Ãô

LD E,(HL)              ;1E77   5E            ^
INC HL                 ;1E78   23            #
LD D,(HL)              ;1E79   56            V
DEC HL                 ;1E7A   2B            +
RET                    ;1E7B   C9            É
CALL 2C39H             ;1E7C   CD 39 2C      Í9,
PUSH HL                ;1E7F   E5            å
LD HL,(47FFH)          ;1E80   2A FF 47      *ÿG
LD A,L                 ;1E83   7D            }
OR H                   ;1E84   B4            ´
JP Z,138EH             ;1E85   CA 8E 13      Ê
XOR A                  ;1E88   AF            ¯
LD (4574H),A           ;1E89   32 74 45      2tE
POP HL                 ;1E8C   E1            á
LD (4801H),HL          ;1E8D   22 01 48      "H
PUSH HL                ;1E90   E5            å
CALL 162DH             ;1E91   CD 2D 16      Í-
CP 22H                 ;1E94   FE 22         þ"
LD DE,1EAFH            ;1E96   11 AF 1E      ¯

JP NZ,1EA9H            ;1E99   C2 A9 1E      Â©

CALL 2383H             ;1E9C   CD 83 23      Í#
CALL 169AH             ;1E9F   CD 9A 16      Í
DEC SP                 ;1EA2   3B            ;
LD (4801H),HL          ;1EA3   22 01 48      "H
CALL 1801H             ;1EA6   CD 01 18      Í
CALL 1EC1H             ;1EA9   CD C1 1E      ÍÁ

JP 1F06H               ;1EAC   C3 06 1F      Ã
CCF                    ;1EAF   3F            ?
JR NZ,1EBFH            ;1EB0   20 0D          
XOR A                  ;1EB2   AF            ¯
LD (1194H),A           ;1EB3   32 94 11      2
RET                    ;1EB6   C9            É
LD A,(457DH)           ;1EB7   3A 7D 45      :}E
OR A                   ;1EBA   B7            ·
CALL Z,0009H           ;1EBB   CC 09 00      Ì	
LD DE,1EAFH            ;1EBE   11 AF 1E      ¯

LD A,(457DH)           ;1EC1   3A 7D 45      :}E
OR A                   ;1EC4   B7            ·
CALL Z,0015H           ;1EC5   CC 15 00      Ì
CALL NZ,1EB2H          ;1EC8   C4 B2 1E      Ä²

LD DE,4455H            ;1ECB   11 55 44      UD
LD A,(1194H)           ;1ECE   3A 94 11      :
CALL 2C7AH             ;1ED1   CD 7A 2C      Íz,
CALL 0003H             ;1ED4   CD 03 00      Í
EX DE,HL               ;1ED7   EB            ë
LD A,(457DH)           ;1ED8   3A 7D 45      :}E
OR A                   ;1EDB   B7            ·
JP NZ,1EF8H            ;1EDC   C2 F8 1E      Âø

LD A,1BH               ;1EDF   3E 1B         >
CP (HL)                ;1EE1   BE            ¾
JP Z,1EFCH             ;1EE2   CA FC 1E      Êü

LD A,0DH               ;1EE5   3E 0D         >
CP (HL)                ;1EE7   BE            ¾
JP Z,1EB7H             ;1EE8   CA B7 1E      Ê·

INC HL                 ;1EEB   23            #
DEC C                  ;1EEC   0D            
JR NZ,1EE7H            ;1EED   20 F8          ø
CALL 168BH             ;1EEF   CD 8B 16      Í
DEC C                  ;1EF2   0D            
RET M                  ;1EF3   F8            ø
LD E,C3H               ;1EF4   1E C3         
Ã
OR A                   ;1EF6   B7            ·
LD E,22H               ;1EF7   1E 22         
"
LD (HL),L              ;1EF9   75            u
LD B,L                 ;1EFA   45            E
RET                    ;1EFB   C9            É
LD A,81H               ;1EFC   3E 81         >
LD (4565H),A           ;1EFE   32 65 45      2eE
POP AF                 ;1F01   F1            ñ
POP HL                 ;1F02   E1            á
JP 1B39H               ;1F03   C3 39 1B      Ã9
LD HL,(4801H)          ;1F06   2A 01 48      *H
CALL 1829H             ;1F09   CD 29 18      Í)
JP Z,1FA4H             ;1F0C   CA A4 1F      Ê¤
CALL 2613H             ;1F0F   CD 13 26      Í&
CALL 2436H             ;1F12   CD 36 24      Í6$
CALL 1829H             ;1F15   CD 29 18      Í)
JR Z,1F1EH             ;1F18   28 04         (
CALL 169AH             ;1F1A   CD 9A 16      Í
INC L                  ;1F1D   2C            ,
LD (4801H),HL          ;1F1E   22 01 48      "H
CALL 197BH             ;1F21   CD 7B 19      Í{
LD HL,(4575H)          ;1F24   2A 75 45      *uE
CALL 168BH             ;1F27   CD 8B 16      Í
INC L                  ;1F2A   2C            ,
DEC L                  ;1F2B   2D            -
RRA                    ;1F2C   1F            
LD (4575H),HL          ;1F2D   22 75 45      "uE
LD A,(457DH)           ;1F30   3A 7D 45      :}E
OR A                   ;1F33   B7            ·
JP NZ,1F3DH            ;1F34   C2 3D 1F      Â=
CALL 1829H             ;1F37   CD 29 18      Í)
CALL Z,1F9AH           ;1F3A   CC 9A 1F      Ì
LD HL,(4575H)          ;1F3D   2A 75 45      *uE
CALL 18C4H             ;1F40   CD C4 18      ÍÄ
LD A,(4574H)           ;1F43   3A 74 45      :tE
OR A                   ;1F46   B7            ·
JP Z,1F4DH             ;1F47   CA 4D 1F      ÊM
LD (4578H),HL          ;1F4A   22 78 45      "xE
LD (4575H),HL          ;1F4D   22 75 45      "uE
LD A,(4571H)           ;1F50   3A 71 45      :qE
OR A                   ;1F53   B7            ·
CALL Z,1F72H           ;1F54   CC 72 1F      Ìr
CALL 1976H             ;1F57   CD 76 19      Ív
CALL 1B6AH             ;1F5A   CD 6A 1B      Íj
SBC A,L                ;1F5D   9D            
INC DE                 ;1F5E   13            
LD A,(457DH)           ;1F5F   3A 7D 45      :}E
OR A                   ;1F62   B7            ·
JP Z,1F06H             ;1F63   CA 06 1F      Ê
LD HL,(4801H)          ;1F66   2A 01 48      *H
CALL 1829H             ;1F69   CD 29 18      Í)
CALL NZ,1EC1H          ;1F6C   C4 C1 1E      ÄÁ

JP 1F06H               ;1F6F   C3 06 1F      Ã
CALL 1801H             ;1F72   CD 01 18      Í
EX DE,HL               ;1F75   EB            ë
CALL 190DH             ;1F76   CD 0D 19      Í

LD A,H                 ;1F79   7C            |
RRA                    ;1F7A   1F            
RET                    ;1F7B   C9            É
POP AF                 ;1F7C   F1            ñ
LD A,(4574H)           ;1F7D   3A 74 45      :tE
OR A                   ;1F80   B7            ·
JP NZ,1398H            ;1F81   C2 98 13      Â
LD A,(457DH)           ;1F84   3A 7D 45      :}E
OR A                   ;1F87   B7            ·
JP NZ,1398H            ;1F88   C2 98 13      Â
LD DE,1318H            ;1F8B   11 18 13      
CALL 1357H             ;1F8E   CD 57 13      ÍW
LD DE,12FFH            ;1F91   11 FF 12      ÿ
CALL 0015H             ;1F94   CD 15 00      Í
JP 1E8CH               ;1F97   C3 8C 1E      Ã

LD A,(4574H)           ;1F9A   3A 74 45      :tE
OR A                   ;1F9D   B7            ·
JP Z,1EB7H             ;1F9E   CA B7 1E      Ê·

JP 1FD4H               ;1FA1   C3 D4 1F      ÃÔ
LD A,(4574H)           ;1FA4   3A 74 45      :tE
OR A                   ;1FA7   B7            ·
JP NZ,19B2H            ;1FA8   C2 B2 19      Â²
POP AF                 ;1FAB   F1            ñ
JP 19B2H               ;1FAC   C3 B2 19      Ã²
LD (4801H),HL          ;1FAF   22 01 48      "H
LD A,(4577H)           ;1FB2   3A 77 45      :wE
OR A                   ;1FB5   B7            ·
CALL Z,1FCAH           ;1FB6   CC CA 1F      ÌÊ
LD HL,(4578H)          ;1FB9   2A 78 45      *xE
LD (4575H),HL          ;1FBC   22 75 45      "uE
XOR A                  ;1FBF   AF            ¯
LD (457DH),A           ;1FC0   32 7D 45      2}E
INC A                  ;1FC3   3C            <
LD (4574H),A           ;1FC4   32 74 45      2tE
JP 1F06H               ;1FC7   C3 06 1F      Ã
INC A                  ;1FCA   3C            <
LD (4577H),A           ;1FCB   32 77 45      2wE
LD HL,4806H            ;1FCE   21 06 48      !H
JP 1FE0H               ;1FD1   C3 E0 1F      Ãà
LD HL,(4575H)          ;1FD4   2A 75 45      *uE
CALL 163DH             ;1FD7   CD 3D 16      Í=
INC HL                 ;1FDA   23            #
CP 3AH                 ;1FDB   FE 3A         þ:
JP Z,1FE9H             ;1FDD   CA E9 1F      Êé
LD A,(HL)              ;1FE0   7E            ~
INC HL                 ;1FE1   23            #
OR (HL)                ;1FE2   B6            ¶
JP Z,1385H             ;1FE3   CA 85 13      Ê

INC HL                 ;1FE6   23            #
INC HL                 ;1FE7   23            #
INC HL                 ;1FE8   23            #
CALL 168BH             ;1FE9   CD 8B 16      Í
ADD A,C                ;1FEC   81            
RST 10H                ;1FED   D7            ×
RRA                    ;1FEE   1F            
LD (4578H),HL          ;1FEF   22 78 45      "xE
LD (4575H),HL          ;1FF2   22 75 45      "uE
RET                    ;1FF5   C9            É
CALL 22AFH             ;1FF6   CD AF 22      Í¯"
CALL 1814H             ;1FF9   CD 14 18      Í
LD DE,(4644H)          ;1FFC   ED 5B 44 46   í[DF
LD A,(DE)              ;2000   1A            
LD DE,0000H            ;2001   11 00 00      
CP C1H                 ;2004   FE C1         þÁ
JP C,2019H             ;2006   DA 19 20      Ú 
SUB D1H                ;2009   D6 D1         ÖÑ
JP NC,2019H            ;200B   D2 19 20      Ò 
LD BC,2019H            ;200E   01 19 20       
PUSH BC                ;2011   C5            Å
PUSH HL                ;2012   E5            å
LD HL,(4644H)          ;2013   2A 44 46      *DF
JP 1963H               ;2016   C3 63 19      Ãc
LD A,(HL)              ;2019   7E            ~
INC HL                 ;201A   23            #
SUB 89H                ;201B   D6 89         Ö
JR Z,2024H             ;201D   28 05         (
CP 02H                 ;201F   FE 02         þ
JP NZ,138EH            ;2021   C2 8E 13      Â
EX AF,AF'              ;2024   08            
LD A,E                 ;2025   7B            {
OR A                   ;2026   B7            ·
JP Z,1B27H             ;2027   CA 27 1B      Ê'
LD A,D                 ;202A   7A            z
OR A                   ;202B   B7            ·
JP NZ,1B27H            ;202C   C2 27 1B      Â'
DEC E                  ;202F   1D            

JP Z,2042H             ;2030   CA 42 20      ÊB 
CALL 1829H             ;2033   CD 29 18      Í)
JP Z,19B8H             ;2036   CA B8 19      Ê¸
CP 2CH                 ;2039   FE 2C         þ,
INC HL                 ;203B   23            #
JP NZ,2033H            ;203C   C2 33 20      Â3 
JP 202FH               ;203F   C3 2F 20      Ã/ 
CALL 16F1H             ;2042   CD F1 16      Íñ
CALL 163DH             ;2045   CD 3D 16      Í=
EX AF,AF'              ;2048   08            
OR A                   ;2049   B7            ·
JP NZ,1CF9H            ;204A   C2 F9 1C      Âù

JP 1CDEH               ;204D   C3 DE 1C      ÃÞ

CALL 2613H             ;2050   CD 13 26      Í&
LD BC,0000H            ;2053   01 00 00      
CP 24H                 ;2056   FE 24         þ$
JR NZ,205CH            ;2058   20 02          
INC HL                 ;205A   23            #
INC B                  ;205B   04            
CALL 169AH             ;205C   CD 9A 16      Í
JR Z,202EH             ;205F   28 CD         (Í
EXX                    ;2061   D9            Ù
JR NZ,2026H            ;2062   20 C2          Â
OR L                   ;2064   B5            µ
JR NZ,204CH            ;2065   20 E5          å
LD HL,(20D7H)          ;2067   2A D7 20      *× 
LD E,H                 ;206A   5C            \
LD D,A                 ;206B   57            W
LD H,A                 ;206C   67            g
INC HL                 ;206D   23            #
INC DE                 ;206E   13            
CALL 16A7H             ;206F   CD A7 16      Í
SUB E                  ;2072   93            
INC DE                 ;2073   13            
LD A,(20D6H)           ;2074   3A D6 20      :Ö 
OR A                   ;2077   B7            ·
POP HL                 ;2078   E1            á
PUSH DE                ;2079   D5            Õ
PUSH HL                ;207A   E5            å
JR NZ,2085H            ;207B   20 08          
LD HL,0005H            ;207D   21 05 00      !
CALL 16A7H             ;2080   CD A7 16      Í
SUB E                  ;2083   93            
INC DE                 ;2084   13            
LD HL,0004H            ;2085   21 04 00      !
ADD HL,DE              ;2088   19            
JP C,1393H             ;2089   DA 93 13      Ú
LD B,H                 ;208C   44            D
LD C,L                 ;208D   4D            M
POP DE                 ;208E   D1            Ñ
CALL 177CH             ;208F   CD 7C 17      Í|
CALL 189CH             ;2092   CD 9C 18      Í
LD HL,(4630H)          ;2095   2A 30 46      *0F
EX DE,HL               ;2098   EB            ë
LD (HL),E              ;2099   73            s
INC HL                 ;209A   23            #
LD (HL),D              ;209B   72            r
INC HL                 ;209C   23            #
LD DE,(20D7H)          ;209D   ED 5B D7 20   í[× 
LD (HL),E              ;20A1   73            s
INC HL                 ;20A2   23            #
LD (HL),D              ;20A3   72            r
INC HL                 ;20A4   23            #
POP BC                 ;20A5   C1            Á
LD A,(20D6H)           ;20A6   3A D6 20      :Ö 
OR A                   ;20A9   B7            ·
JP Z,20C1H             ;20AA   CA C1 20      ÊÁ 
LD (HL),0DH            ;20AD   36 0D         6
INC HL                 ;20AF   23            #
DEC BC                 ;20B0   0B            

LD A,B                 ;20B1   78            x
OR C                   ;20B2   B1            ±
JR NZ,20ADH            ;20B3   20 F8          ø
LD HL,(20D4H)          ;20B5   2A D4 20      *Ô 
CALL 168BH             ;20B8   CD 8B 16      Í
INC L                  ;20BB   2C            ,
OR L                   ;20BC   B5            µ
ADD HL,DE              ;20BD   19            
JP 2050H               ;20BE   C3 50 20      ÃP 
EX DE,HL               ;20C1   EB            ë
PUSH BC                ;20C2   C5            Å
LD HL,1619H            ;20C3   21 19 16      !
LD BC,0005H            ;20C6   01 05 00      
LDIR                   ;20C9   ED B0         í°
POP BC                 ;20CB   C1            Á
DEC BC                 ;20CC   0B            

LD A,B                 ;20CD   78            x
OR C                   ;20CE   B1            ±
JR NZ,20C2H            ;20CF   20 F1          ñ
JP 20B5H               ;20D1   C3 B5 20      Ãµ 
DEC HL                 ;20D4   2B            +
AND E                  ;20D5   A3            £
INC SP                 ;20D6   33            3
LD A,9EH               ;20D7   3E 9E         >
PUSH DE                ;20D9   D5            Õ
PUSH BC                ;20DA   C5            Å
CALL 19A9H             ;20DB   CD A9 19      Í©
POP BC                 ;20DE   C1            Á
LD A,(HL)              ;20DF   7E            ~
CP 2CH                 ;20E0   FE 2C         þ,
CALL Z,215AH           ;20E2   CC 5A 21      ÌZ!
CALL 169AH             ;20E5   CD 9A 16      Í
ADD HL,HL              ;20E8   29            )
LD (20D4H),HL          ;20E9   22 D4 20      "Ô 
POP HL                 ;20EC   E1            á
LD (4630H),HL          ;20ED   22 30 46      "0F
EX DE,HL               ;20F0   EB            ë
LD (20D7H),HL          ;20F1   22 D7 20      "× 
LD A,B                 ;20F4   78            x
LD (20D6H),A           ;20F5   32 D6 20      2Ö 
LD HL,4636H            ;20F8   21 36 46      !6F
LD DE,0006H            ;20FB   11 06 00      
OR A                   ;20FE   B7            ·
JR NZ,2102H            ;20FF   20 01          
ADD HL,DE              ;2101   19            
LD A,C                 ;2102   79            y
LD E,02H               ;2103   1E 02         

OR A                   ;2105   B7            ·
JR NZ,2109H            ;2106   20 01          
ADD HL,DE              ;2108   19            
LD E,(HL)              ;2109   5E            ^
INC HL                 ;210A   23            #
LD D,(HL)              ;210B   56            V
EX DE,HL               ;210C   EB            ë
CALL 17C4H             ;210D   CD C4 17      ÍÄ
LD B,E                 ;2110   43            C
LD HL,45CAH            ;2111   21 CA 45      !ÊE
LD HL,235EH            ;2114   21 5E 23      !^#
PUSH HL                ;2117   E5            å
LD L,(HL)              ;2118   6E            n
LD D,00H               ;2119   16 00         
LD H,D                 ;211B   62            b
INC HL                 ;211C   23            #
INC DE                 ;211D   13            
CALL 16C8H             ;211E   CD C8 16      ÍÈ
LD A,(20D6H)           ;2121   3A D6 20      :Ö 
OR A                   ;2124   B7            ·
JP NZ,2134H            ;2125   C2 34 21      Â4!
LD HL,0005H            ;2128   21 05 00      !
CALL 16C8H             ;212B   CD C8 16      ÍÈ
POP HL                 ;212E   E1            á
ADD HL,DE              ;212F   19            
INC HL                 ;2130   23            #
JP 210DH               ;2131   C3 0D 21      Ã
!
POP HL                 ;2134   E1            á
LD A,0DH               ;2135   3E 0D         >
INC HL                 ;2137   23            #
CP (HL)                ;2138   BE            ¾
JR NZ,2137H            ;2139   20 FC          ü
DEC DE                 ;213B   1B            
LD A,D                 ;213C   7A            z
OR E                   ;213D   B3            ³
JR NZ,2135H            ;213E   20 F5          õ
JP 2130H               ;2140   C3 30 21      Ã0!
XOR A                  ;2143   AF            ¯
RET                    ;2144   C9            É
LD C,(HL)              ;2145   4E            N
INC HL                 ;2146   23            #
LD B,(HL)              ;2147   46            F
INC HL                 ;2148   23            #
LD DE,(20D7H)          ;2149   ED 5B D7 20   í[× 
LD A,B                 ;214D   78            x
CP D                   ;214E   BA            º
JR C,2153H             ;214F   38 02         8
LD A,C                 ;2151   79            y
CP E                   ;2152   BB            »
JP C,138EH             ;2153   DA 8E 13      Ú
LD A,01H               ;2156   3E 01         >
OR A                   ;2158   B7            ·
RET                    ;2159   C9            É
INC C                  ;215A   0C            

PUSH BC                ;215B   C5            Å
PUSH DE                ;215C   D5            Õ
INC HL                 ;215D   23            #
CALL 19A9H             ;215E   CD A9 19      Í©
LD A,E                 ;2161   7B            {
POP DE                 ;2162   D1            Ñ
LD D,A                 ;2163   57            W
POP BC                 ;2164   C1            Á
RET                    ;2165   C9            É
CALL 198CH             ;2166   CD 8C 19      Í
PUSH DE                ;2169   D5            Õ
CALL 169AH             ;216A   CD 9A 16      Í
INC L                  ;216D   2C            ,
CALL 19A9H             ;216E   CD A9 19      Í©
EX (SP),HL             ;2171   E3            ã
LD (HL),E              ;2172   73            s
POP HL                 ;2173   E1            á
JP 19B5H               ;2174   C3 B5 19      Ãµ
PUSH HL                ;2177   E5            å
CALL 1857H             ;2178   CD 57 18      ÍW
CALL 1872H             ;217B   CD 72 18      Ír
POP HL                 ;217E   E1            á
JP 19B5H               ;217F   C3 B5 19      Ãµ
CALL 2258H             ;2182   CD 58 22      ÍX"
CALL 1814H             ;2185   CD 14 18      Í
LD IX,(4644H)          ;2188   DD 2A 44 46   Ý*DF
BIT 7,(IX+4H)          ;218C   DD CB 04 7E   ÝË~
JP Z,19C7H             ;2190   CA C7 19      ÊÇ
LD A,(HL)              ;2193   7E            ~
INC HL                 ;2194   23            #
CP 89H                 ;2195   FE 89         þ
JP Z,1CDBH             ;2197   CA DB 1C      ÊÛ

CP 8BH                 ;219A   FE 8B         þ
JP Z,1CF6H             ;219C   CA F6 1C      Êö

CP ADH                 ;219F   FE AD         þ­
JP NZ,138EH            ;21A1   C2 8E 13      Â
CALL 1659H             ;21A4   CD 59 16      ÍY
JP C,1CDBH             ;21A7   DA DB 1C      ÚÛ

LD (4801H),HL          ;21AA   22 01 48      "H
JP 19E1H               ;21AD   C3 E1 19      Ãá
CALL 162DH             ;21B0   CD 2D 16      Í-
SUB 41H                ;21B3   D6 41         ÖA
CP 1AH                 ;21B5   FE 1A         þ
JP NC,138EH            ;21B7   D2 8E 13      Ò
LD E,(HL)              ;21BA   5E            ^
INC HL                 ;21BB   23            #
CALL 169AH             ;21BC   CD 9A 16      Í
JR Z,2197H             ;21BF   28 D6         (Ö
LD B,C                 ;21C1   41            A
CP 1AH                 ;21C2   FE 1A         þ
JP NC,138EH            ;21C4   D2 8E 13      Ò
LD D,(HL)              ;21C7   56            V
INC HL                 ;21C8   23            #
CALL 169AH             ;21C9   CD 9A 16      Í
ADD HL,HL              ;21CC   29            )
CALL 169AH             ;21CD   CD 9A 16      Í
OR (HL)                ;21D0   B6            ¶
PUSH HL                ;21D1   E5            å
CALL 163DH             ;21D2   CD 3D 16      Í=
POP BC                 ;21D5   C1            Á
PUSH HL                ;21D6   E5            å
XOR A                  ;21D7   AF            ¯
SBC HL,BC              ;21D8   ED 42         íB
PUSH BC                ;21DA   C5            Å
PUSH HL                ;21DB   E5            å
LD HL,(4634H)          ;21DC   2A 34 46      *4F
LD A,(HL)              ;21DF   7E            ~
CP E                   ;21E0   BB            »
JP Z,2204H             ;21E1   CA 04 22      Ê"
CP 00H                 ;21E4   FE 00         þ
JR Z,21EFH             ;21E6   28 07         (
INC HL                 ;21E8   23            #
INC HL                 ;21E9   23            #
CALL 1633H             ;21EA   CD 33 16      Í3
JR 21DFH               ;21ED   18 F0         ð
EX DE,HL               ;21EF   EB            ë
LD BC,0003H            ;21F0   01 03 00      
CALL 177CH             ;21F3   CD 7C 17      Í|
CALL 189CH             ;21F6   CD 9C 18      Í
EX DE,HL               ;21F9   EB            ë
LD (HL),E              ;21FA   73            s
INC HL                 ;21FB   23            #
LD (HL),D              ;21FC   72            r
INC HL                 ;21FD   23            #
LD (HL),0DH            ;21FE   36 0D         6
EX DE,HL               ;2200   EB            ë
JP 221AH               ;2201   C3 1A 22      Ã"
INC HL                 ;2204   23            #
LD (HL),D              ;2205   72            r
INC HL                 ;2206   23            #
PUSH HL                ;2207   E5            å
CALL 163DH             ;2208   CD 3D 16      Í=
POP DE                 ;220B   D1            Ñ
XOR A                  ;220C   AF            ¯
SBC HL,DE              ;220D   ED 52         íR
LD B,H                 ;220F   44            D
LD C,L                 ;2210   4D            M
CALL 1766H             ;2211   CD 66 17      Íf
CALL 1651H             ;2214   CD 51 16      ÍQ
CALL 189CH             ;2217   CD 9C 18      Í
POP BC                 ;221A   C1            Á
POP HL                 ;221B   E1            á
CALL 1796H             ;221C   CD 96 17      Í
CALL 189CH             ;221F   CD 9C 18      Í
POP HL                 ;2222   E1            á
JP 19B5H               ;2223   C3 B5 19      Ãµ
CALL 1829H             ;2226   CD 29 18      Í)
JP Z,19B5H             ;2229   CA B5 19      Êµ
CALL 22AFH             ;222C   CD AF 22      Í¯"
CALL 1829H             ;222F   CD 29 18      Í)
JR Z,2235H             ;2232   28 01         (
INC HL                 ;2234   23            #
PUSH HL                ;2235   E5            å
CALL 180FH             ;2236   CD 0F 18      Í
CALL 1801H             ;2239   CD 01 18      Í
CALL 0030H             ;223C   CD 30 00      Í0
JP C,1385H             ;223F   DA 85 13      Ú

POP HL                 ;2242   E1            á
JP 2226H               ;2243   C3 26 22      Ã&"
CALL 19A9H             ;2246   CD A9 19      Í©
LD A,E                 ;2249   7B            {
DEC A                  ;224A   3D            =
CP 07H                 ;224B   FE 07         þ
JP NC,1398H            ;224D   D2 98 13      Ò
INC A                  ;2250   3C            <
CALL 0041H             ;2251   CD 41 00      ÍA
JP 1B27H               ;2254   C3 27 1B      Ã'
INC HL                 ;2257   23            #
CALL 22AFH             ;2258   CD AF 22      Í¯"
CP B0H                 ;225B   FE B0         þ°
RET C                  ;225D   D8            Ø
CP BCH                 ;225E   FE BC         þ¼
RET NC                 ;2260   D0            Ð
EX AF,AF'              ;2261   08            
LD A,D                 ;2262   7A            z
OR A                   ;2263   B7            ·
JP NZ,2272H            ;2264   C2 72 22      Âr"
EX AF,AF'              ;2267   08            
EXX                    ;2268   D9            Ù
LD BC,225BH            ;2269   01 5B 22      ["
LD DE,22AEH            ;226C   11 AE 22      ®"
JP 2339H               ;226F   C3 39 23      Ã9#
EX AF,AF'              ;2272   08            
CP B6H                 ;2273   FE B6         þ¶
JP NZ,138EH            ;2275   C2 8E 13      Â
LD A,C                 ;2278   79            y
PUSH DE                ;2279   D5            Õ
PUSH AF                ;227A   F5            õ
CALL 22AEH             ;227B   CD AE 22      Í®"
CALL 180FH             ;227E   CD 0F 18      Í
POP AF                 ;2281   F1            ñ
EX (SP),HL             ;2282   E3            ã
LD B,A                 ;2283   47            G
SUB C                  ;2284   91            
JP NZ,22A1H            ;2285   C2 A1 22      Â¡"
OR B                   ;2288   B0            °
JP Z,229CH             ;2289   CA 9C 22      Ê"
CALL 1801H             ;228C   CD 01 18      Í
EX DE,HL               ;228F   EB            ë
CALL 1801H             ;2290   CD 01 18      Í
LD A,(DE)              ;2293   1A            
CP (HL)                ;2294   BE            ¾
INC HL                 ;2295   23            #
INC DE                 ;2296   13            
JP NZ,22A1H            ;2297   C2 A1 22      Â¡"
DJNZ 2293H             ;229A   10 F7         ÷
LD DE,161EH            ;229C   11 1E 16
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
